Klesp0/Bigtendo-Handheld-SBC/Design/Assets/images/Breakout/breakout_bg.png

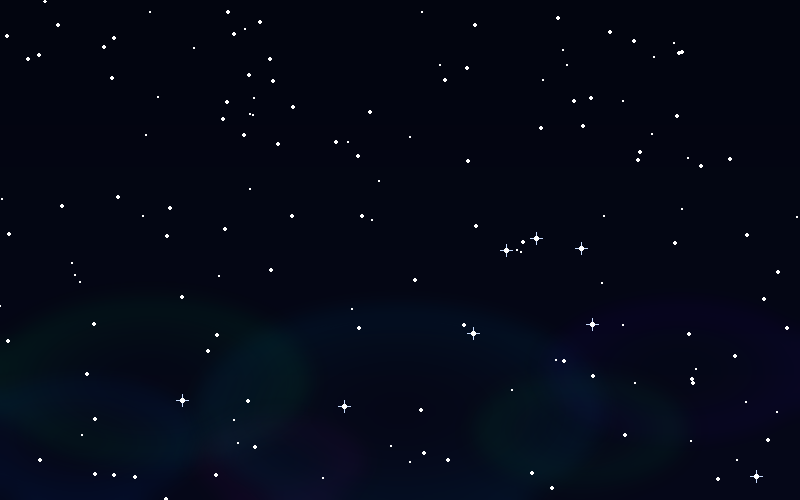
Design/Assets/images/Breakout/breakout_bg.png
