Klesp0/Bigtendo-Handheld-SBC/Design/Assets/images/memory/memory_bg.png

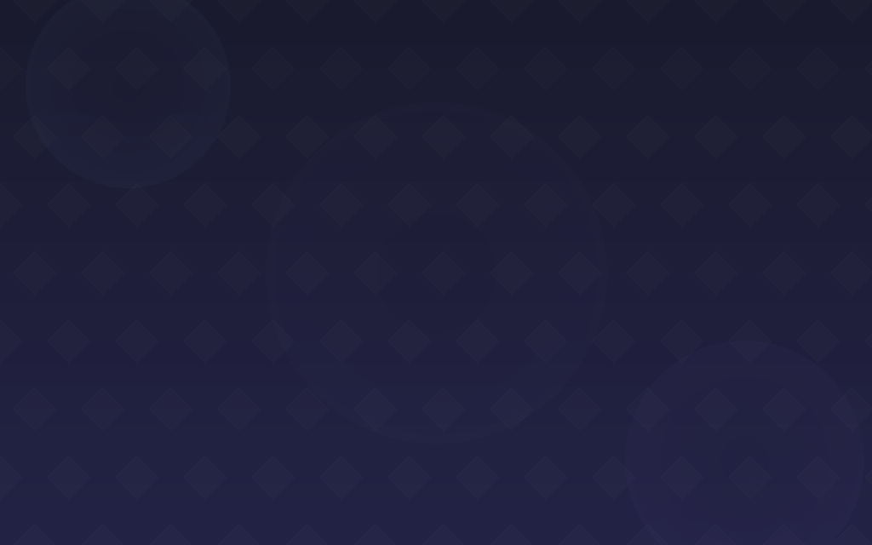
Design/Assets/images/memory/memory_bg.png
