Klesp0/Bigtendo-Handheld-SBC/Media/images/1_ups.png

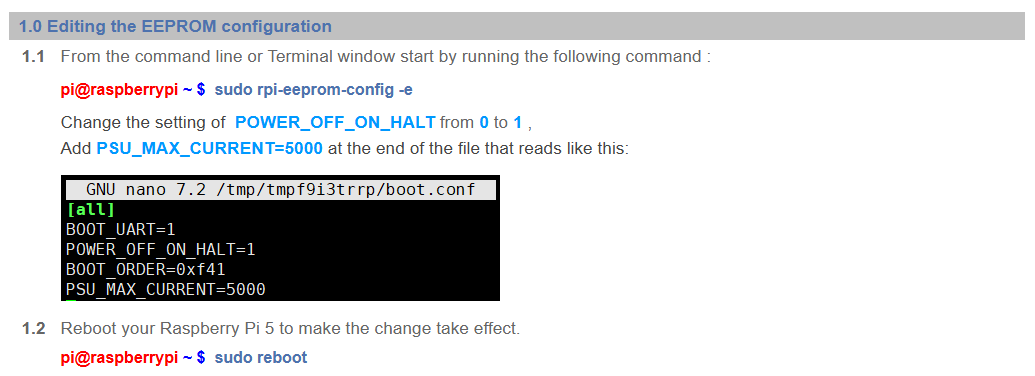
Media/images/1_ups.png
