Klesp0/Bigtendo-Handheld-SBC/Media/images/2_ups.png

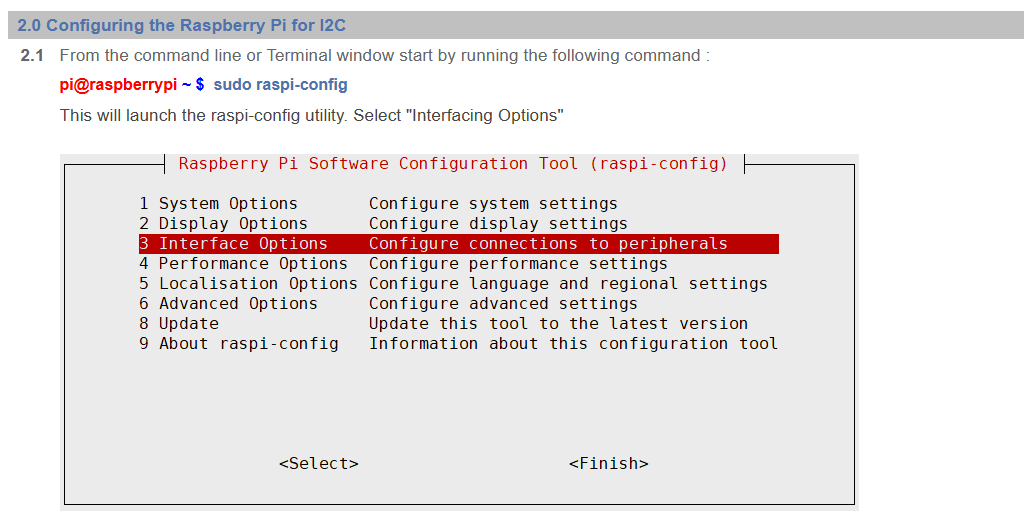
Media/images/2_ups.png
