Klesp0/Bigtendo-Handheld-SBC/Media/images/3_ups.png

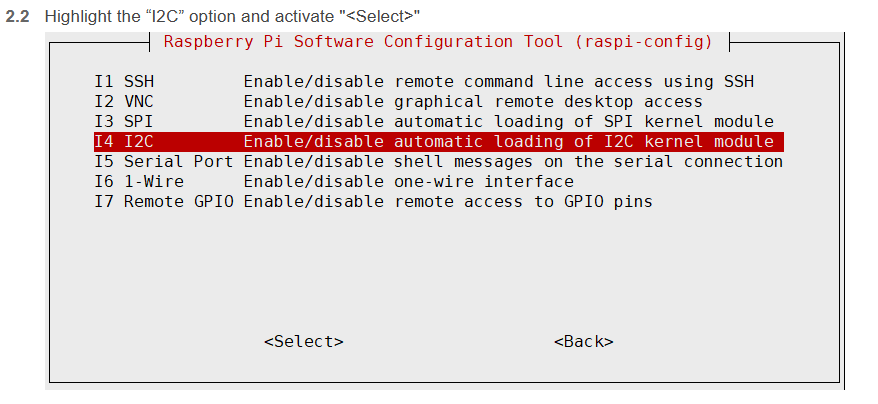
Media/images/3_ups.png
