Klesp0/Bigtendo-Handheld-SBC/Media/images/4_ups.png

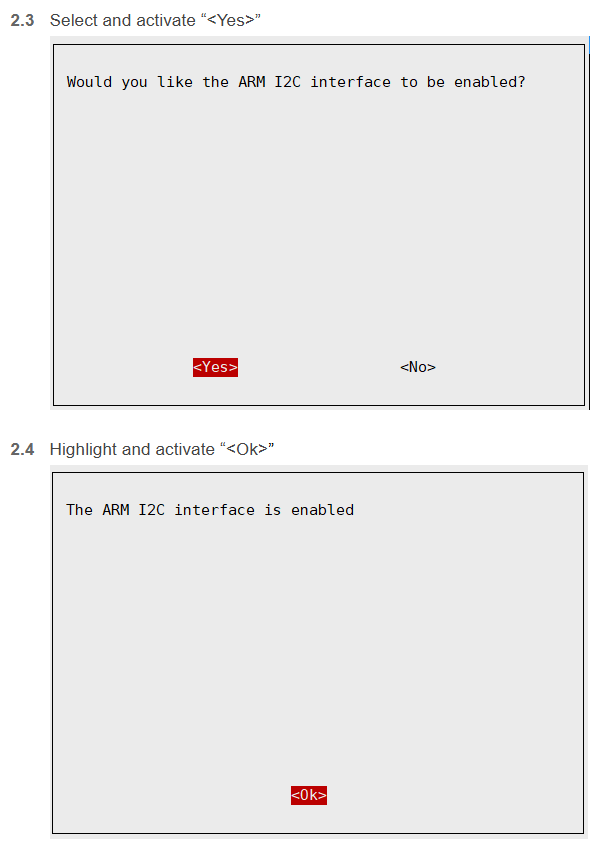
Media/images/4_ups.png
