Klesp0/Bigtendo-Handheld-SBC/Media/images/5_ups.png

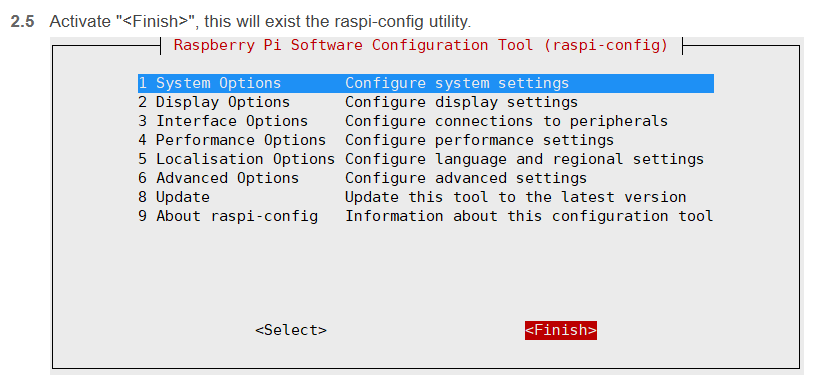
Media/images/5_ups.png
