Klesp0/Bigtendo-Handheld-SBC/Media/images/6_ups.png

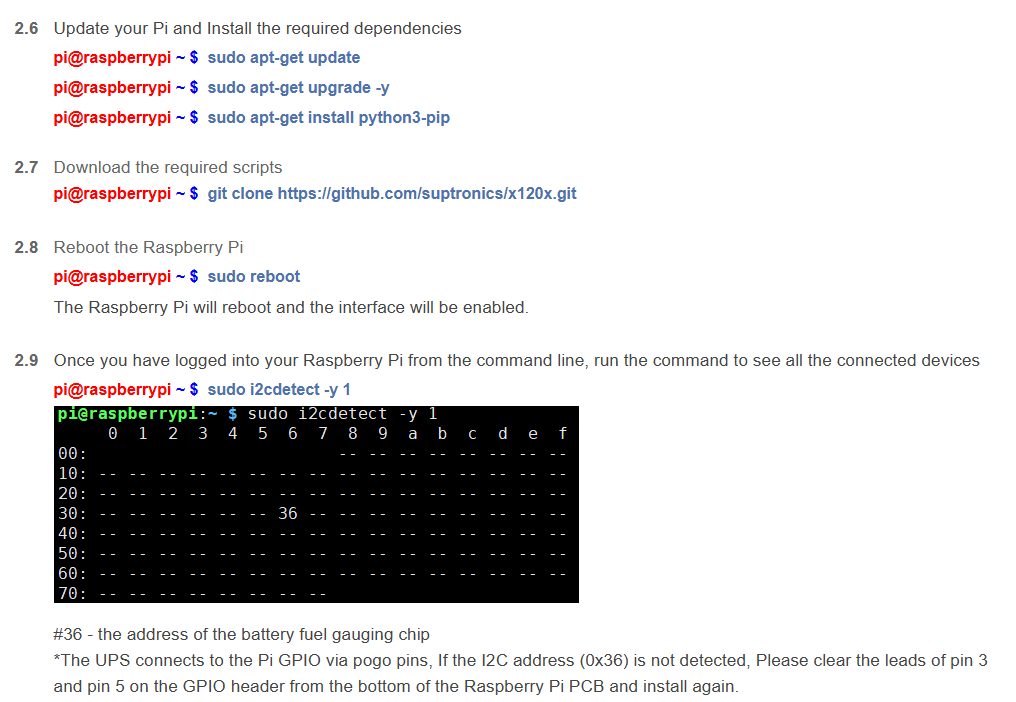
Media/images/6_ups.png
