Klesp0/Bigtendo-Handheld-SBC/Media/images/7_ups.png

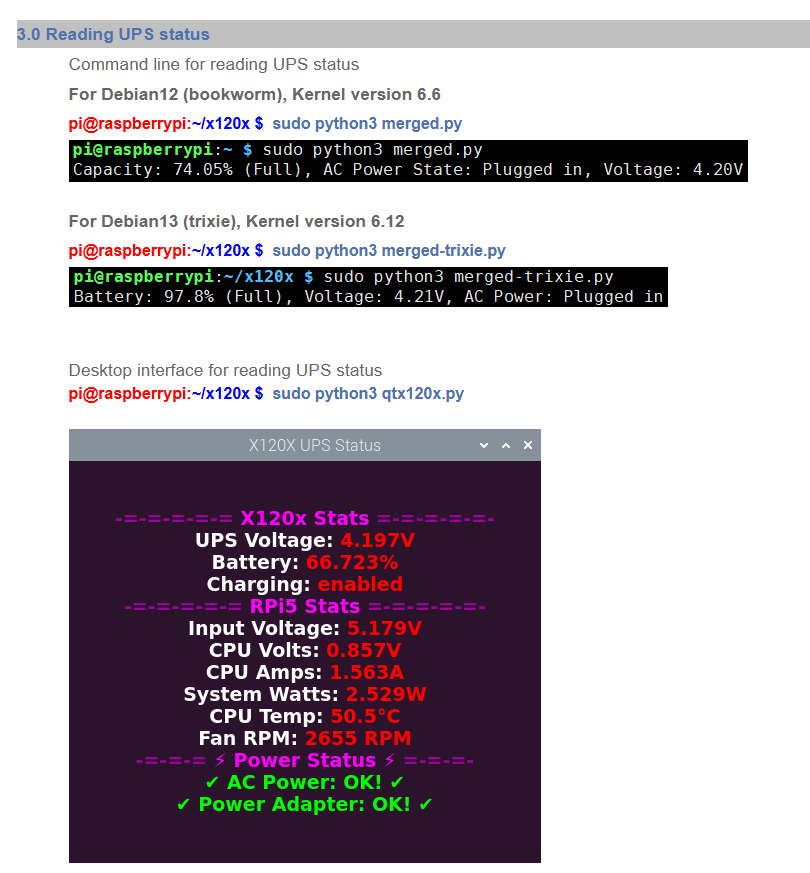
Media/images/7_ups.png
