Klesp0/Bigtendo-Handheld-SBC/Media/images/8_ups.png

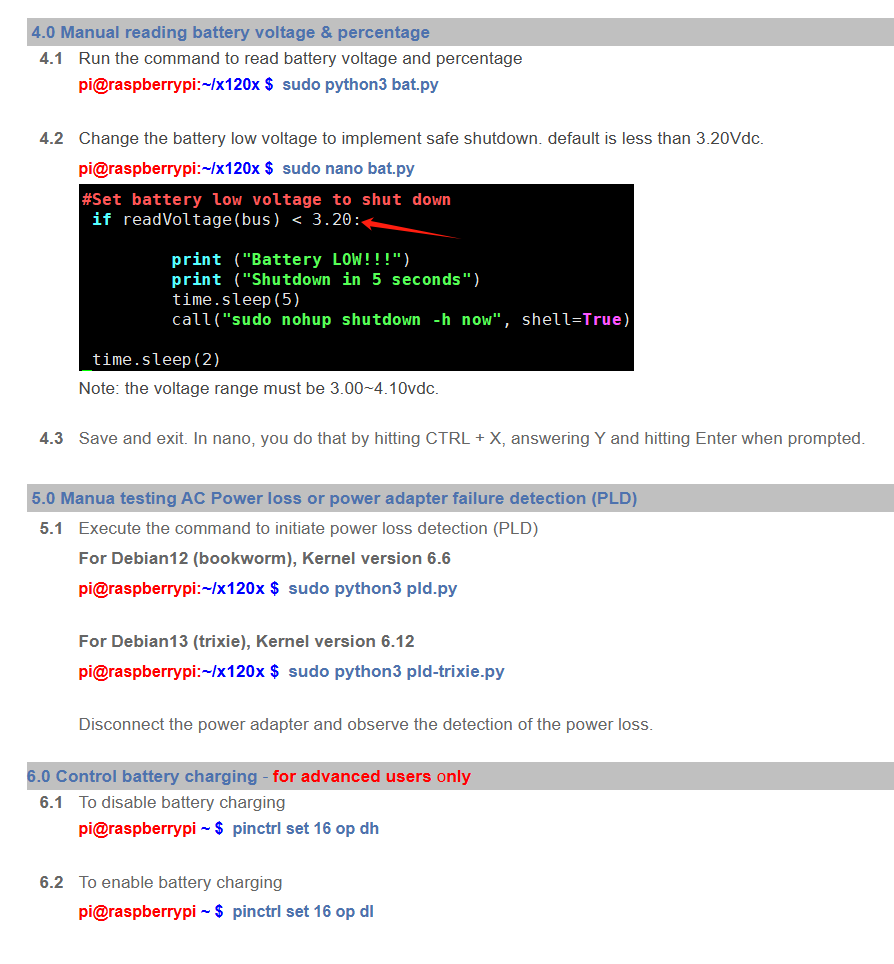
Media/images/8_ups.png
