Klesp0/Bigtendo-Handheld-SBC/Media/images/chuck.jpg

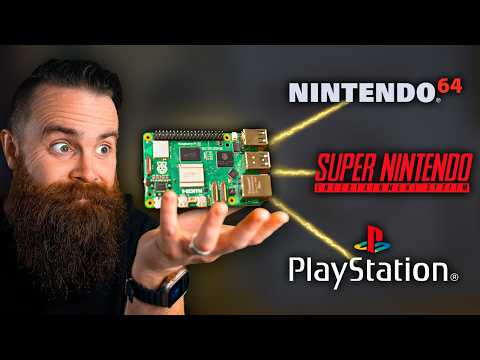
Media/images/chuck.jpg
