Klesp0/Bigtendo-Handheld-SBC/Media/images/imager.png

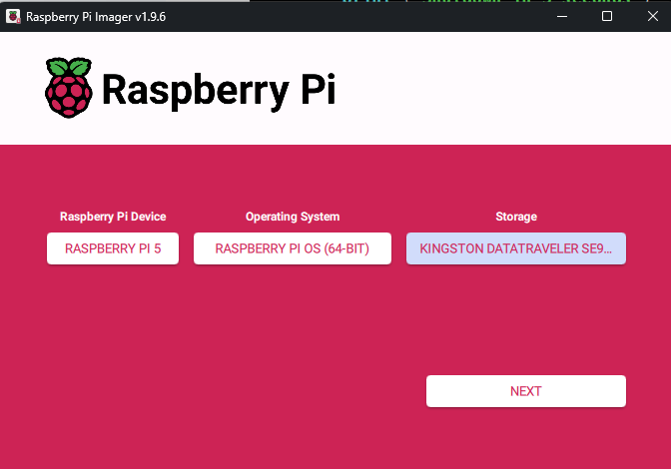
Media/images/imager.png
