Klesp0/Bigtendo-Handheld-SBC/Media/images/Rpi5_pinout.png

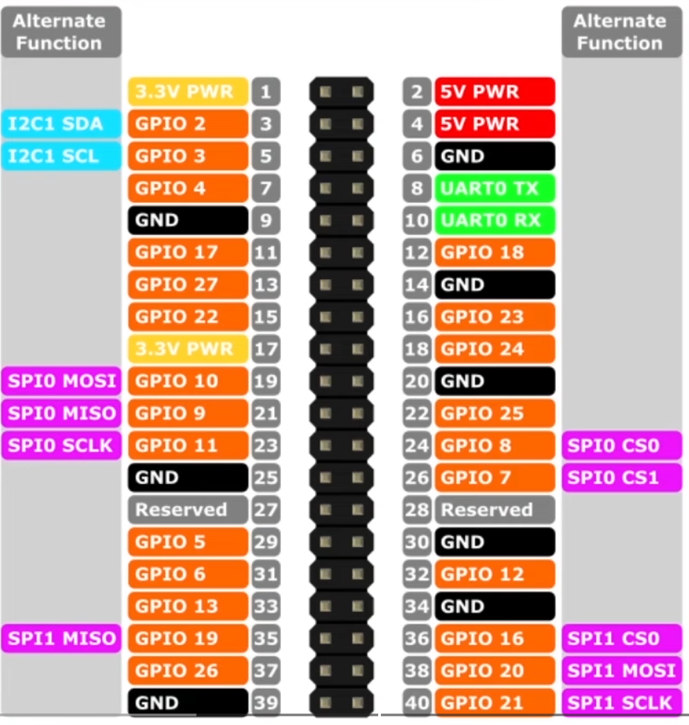
Media/images/Rpi5_pinout.png
