Klesp0/Bigtendo-Handheld-SBC/Media/images/Screenshot 2025-12-04 223239.png

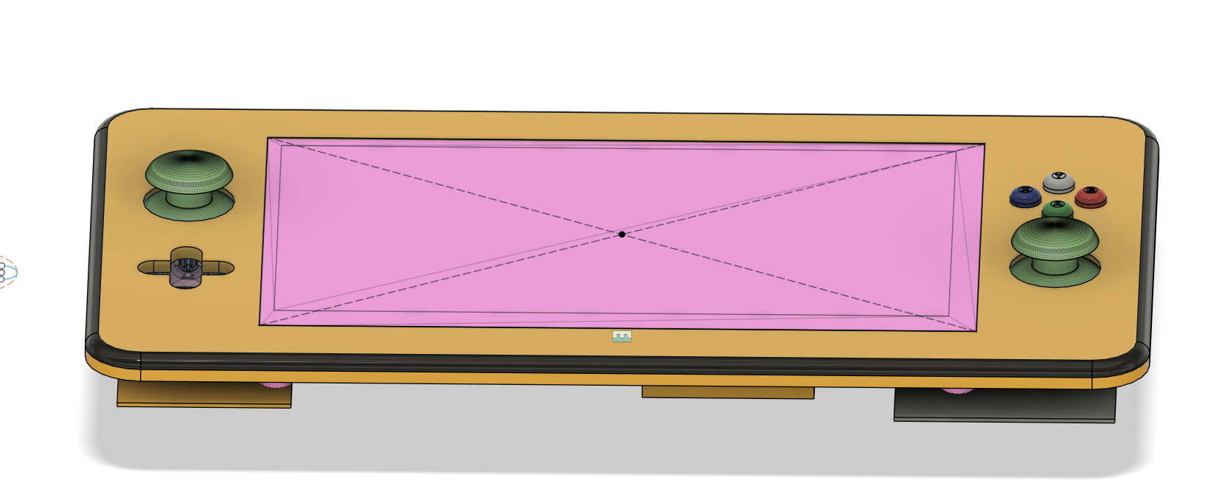
Media/images/Screenshot 2025-12-04 223239.png
