Klesp0/Bigtendo-Handheld-SBC/Media/photos/0d159862-bd19-4e7a-ac6c-457c6c9c0e92.jpg

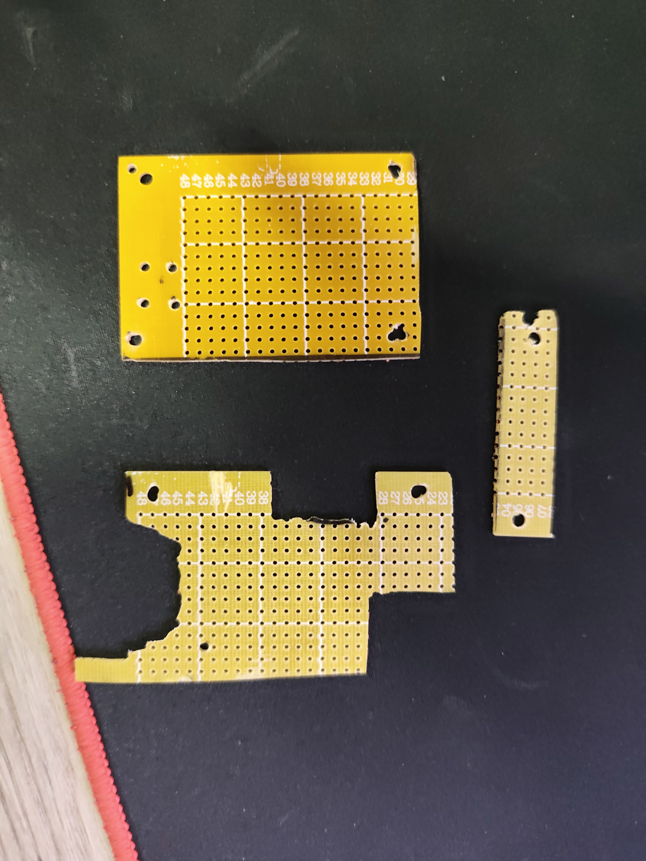
Media/photos/0d159862-bd19-4e7a-ac6c-457c6c9c0e92.jpg
