Klesp0/Bigtendo-Handheld-SBC/Media/photos/1a0360f3-a38d-4172-a27d-07ee18a2b8d9(1).jpg

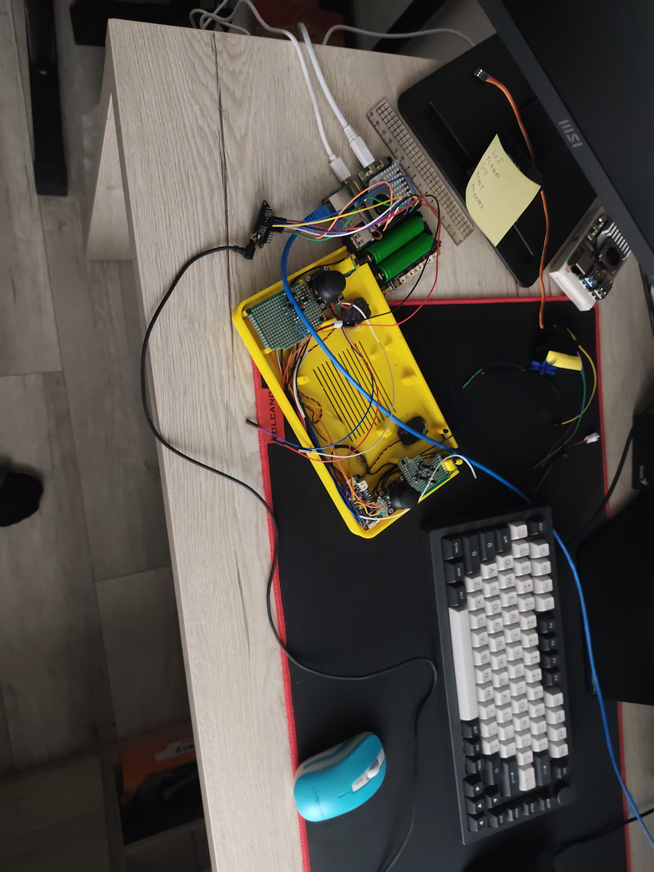
Media/photos/1a0360f3-a38d-4172-a27d-07ee18a2b8d9(1).jpg
