Klesp0/Bigtendo-Handheld-SBC/Media/photos/2c9164c2-df41-48e4-916f-fafe2159fc4d.jpg

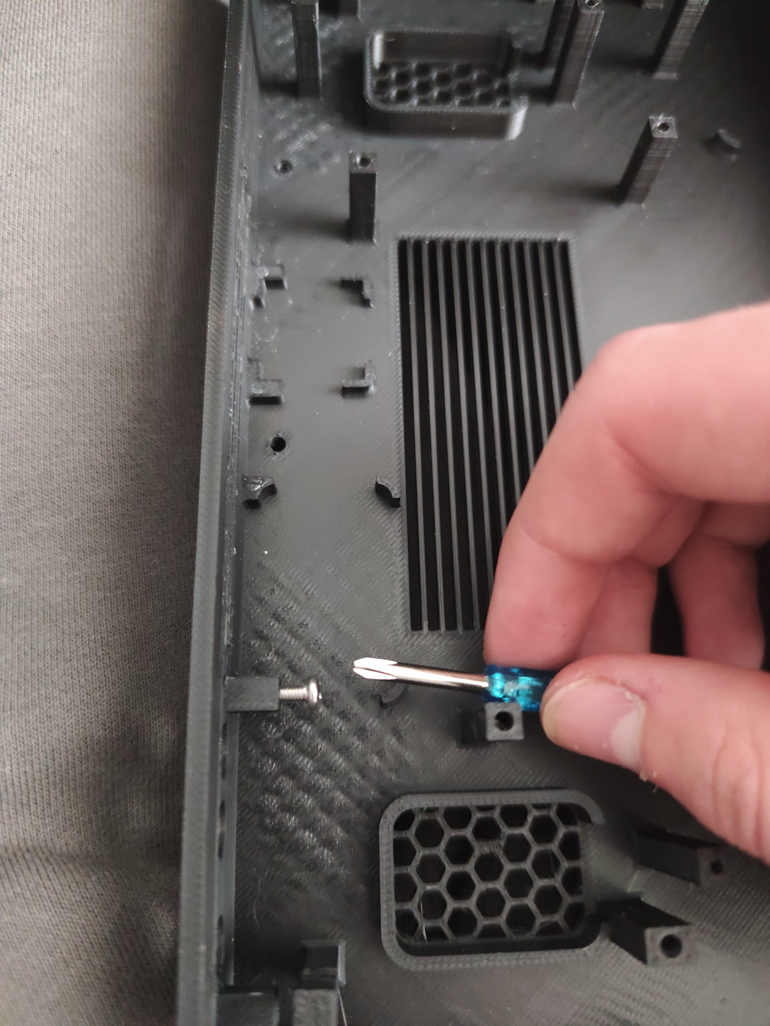
Media/photos/2c9164c2-df41-48e4-916f-fafe2159fc4d.jpg
