Klesp0/Bigtendo-Handheld-SBC/Media/photos/5aacf961-113f-42dd-8feb-71a53d698393.jpg

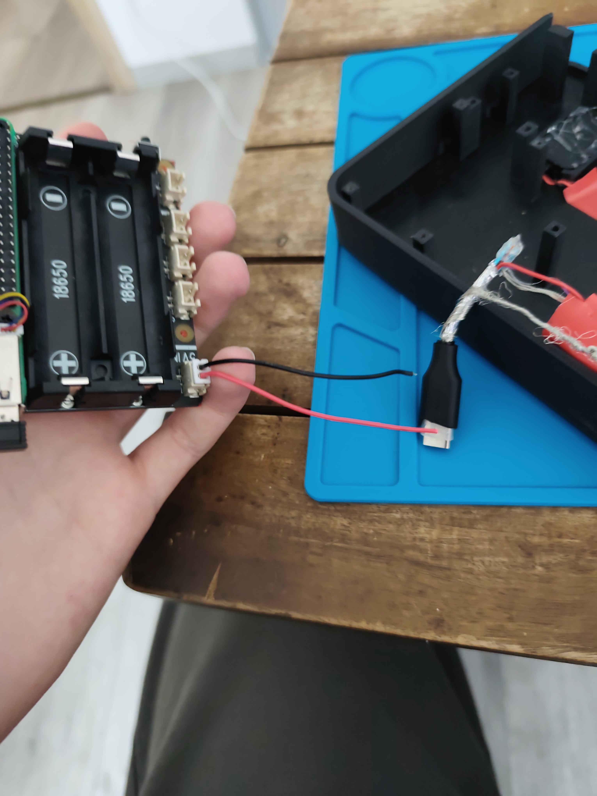
Media/photos/5aacf961-113f-42dd-8feb-71a53d698393.jpg
