Klesp0/Bigtendo-Handheld-SBC/Media/photos/5e09d375-d419-4c3d-b2d1-73679d527c42.jpg

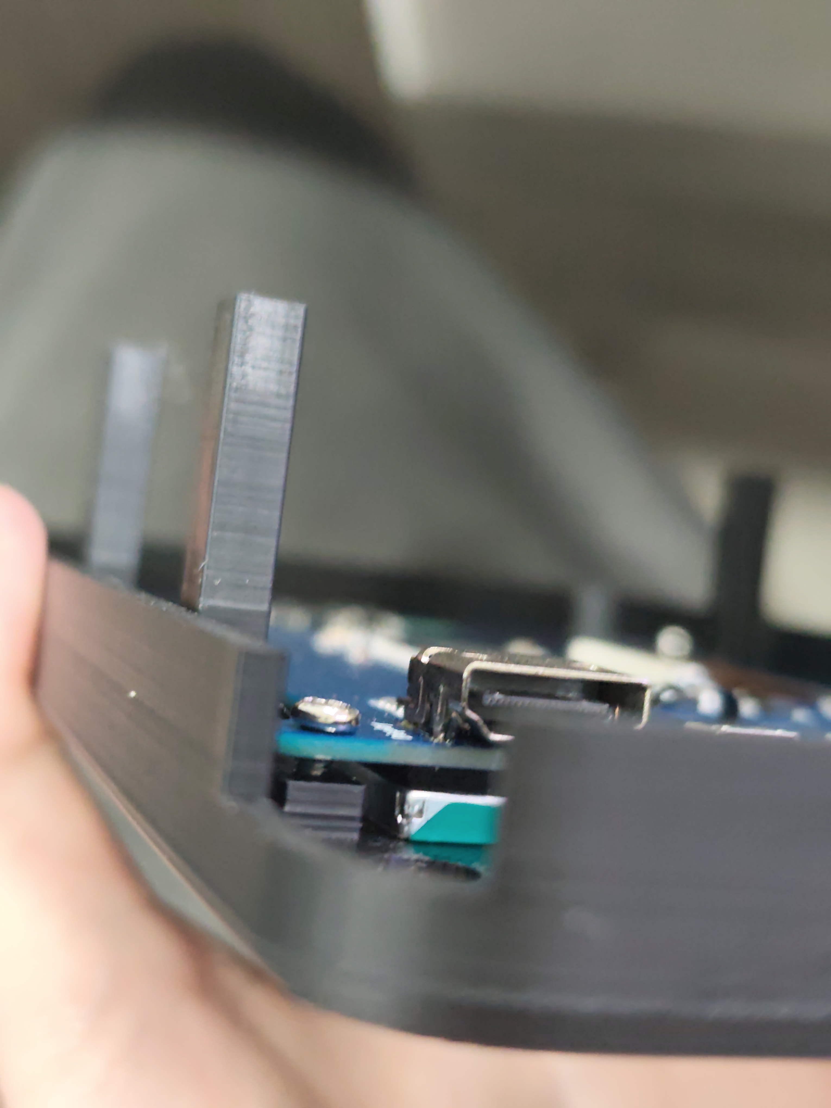
Media/photos/5e09d375-d419-4c3d-b2d1-73679d527c42.jpg
