Klesp0/Bigtendo-Handheld-SBC/Media/photos/6e5a2ec0-2364-49f0-92fe-5897d2cda284.jpg

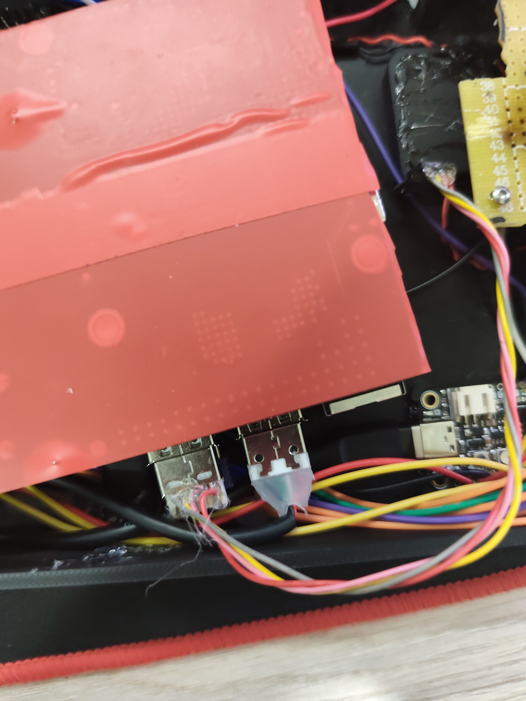
Media/photos/6e5a2ec0-2364-49f0-92fe-5897d2cda284.jpg
