Klesp0/Bigtendo-Handheld-SBC/Media/photos/6e945cf3-38ae-4828-a9d3-f2ff966455ae.jpg

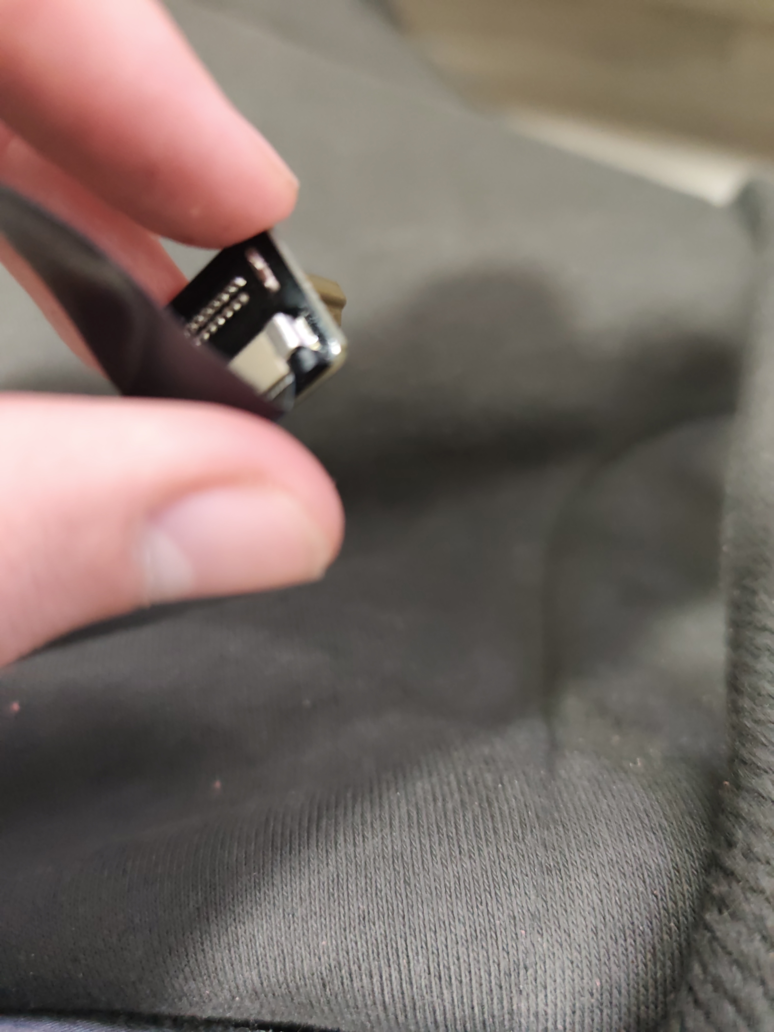
Media/photos/6e945cf3-38ae-4828-a9d3-f2ff966455ae.jpg
