Klesp0/Bigtendo-Handheld-SBC/Media/photos/46b99d0f-3195-408c-8193-283539404b6c.jpg

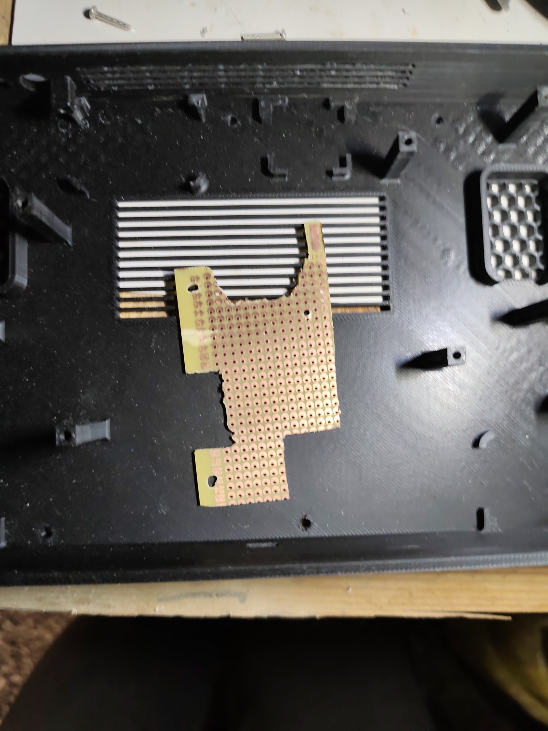
Media/photos/46b99d0f-3195-408c-8193-283539404b6c.jpg
