Klesp0/Bigtendo-Handheld-SBC/Media/photos/55b0e54c-f542-49ae-9d47-5be7d64822e2.jpg

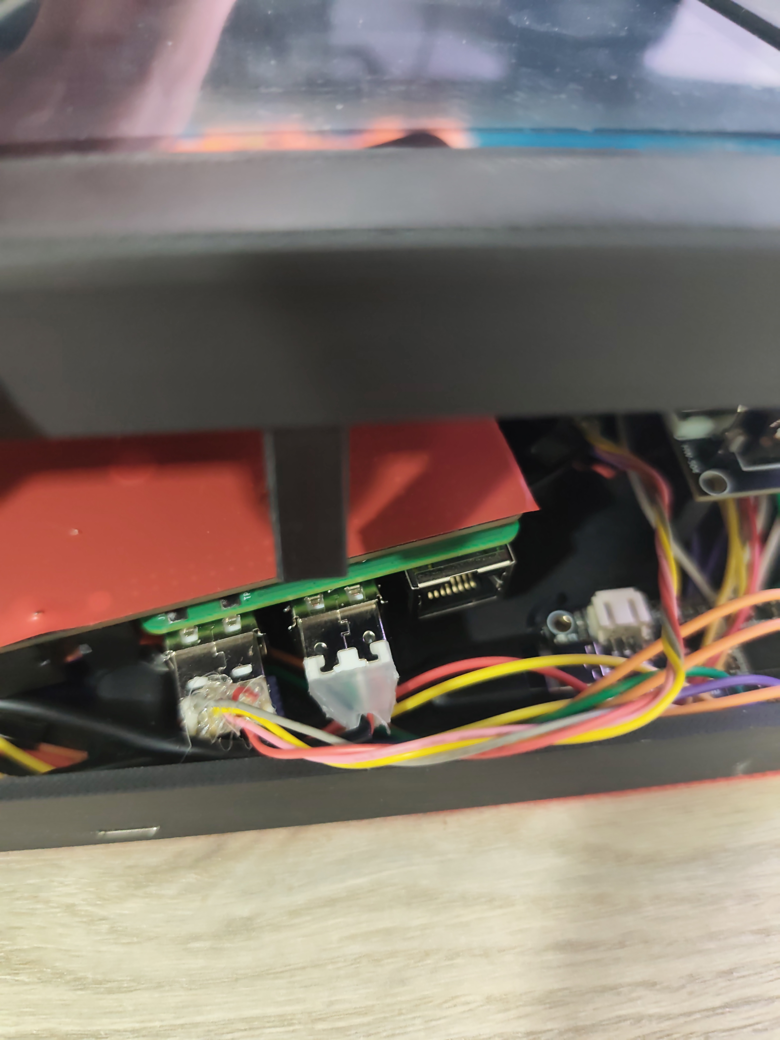
Media/photos/55b0e54c-f542-49ae-9d47-5be7d64822e2.jpg
