Klesp0/Bigtendo-Handheld-SBC/Media/photos/63fe22ae-a2fc-4c9e-bf27-66a3d39b91c6.jpg

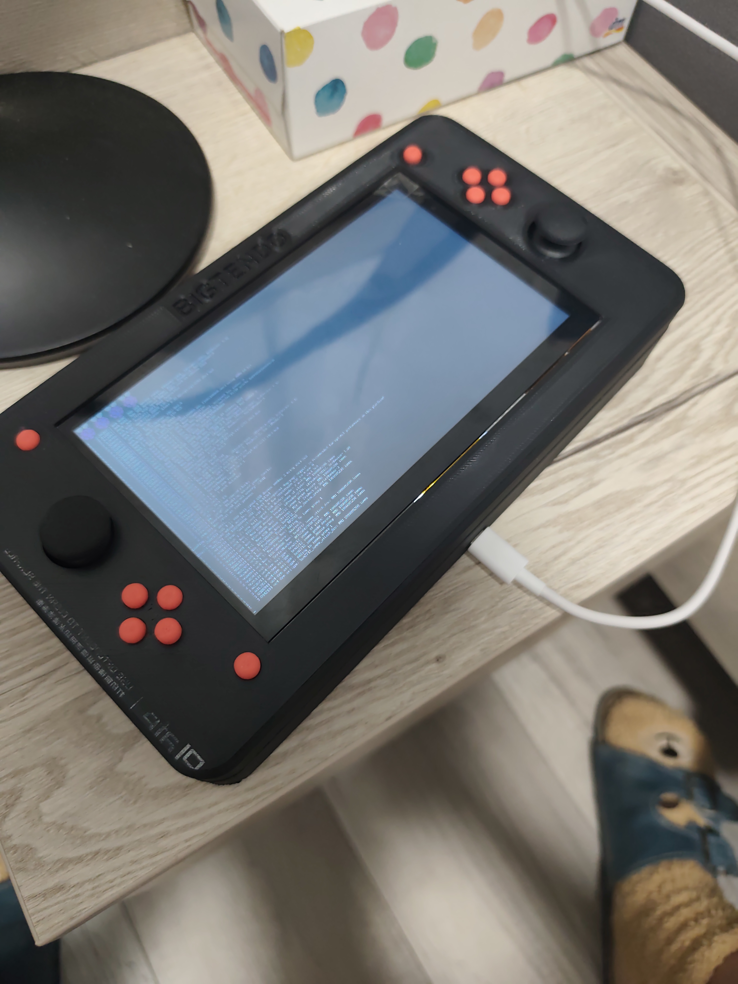
Media/photos/63fe22ae-a2fc-4c9e-bf27-66a3d39b91c6.jpg
