Klesp0/Bigtendo-Handheld-SBC/Media/photos/68ed0358-8793-4e74-b9dc-9e63b9d81c03.jpg

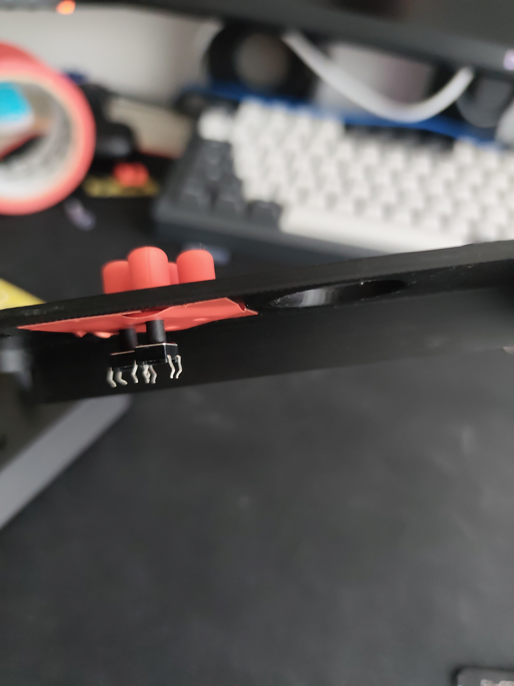
Media/photos/68ed0358-8793-4e74-b9dc-9e63b9d81c03.jpg
