Klesp0/Bigtendo-Handheld-SBC/Media/photos/849dee18-2907-47e5-b8df-e42aead211ff.jpg

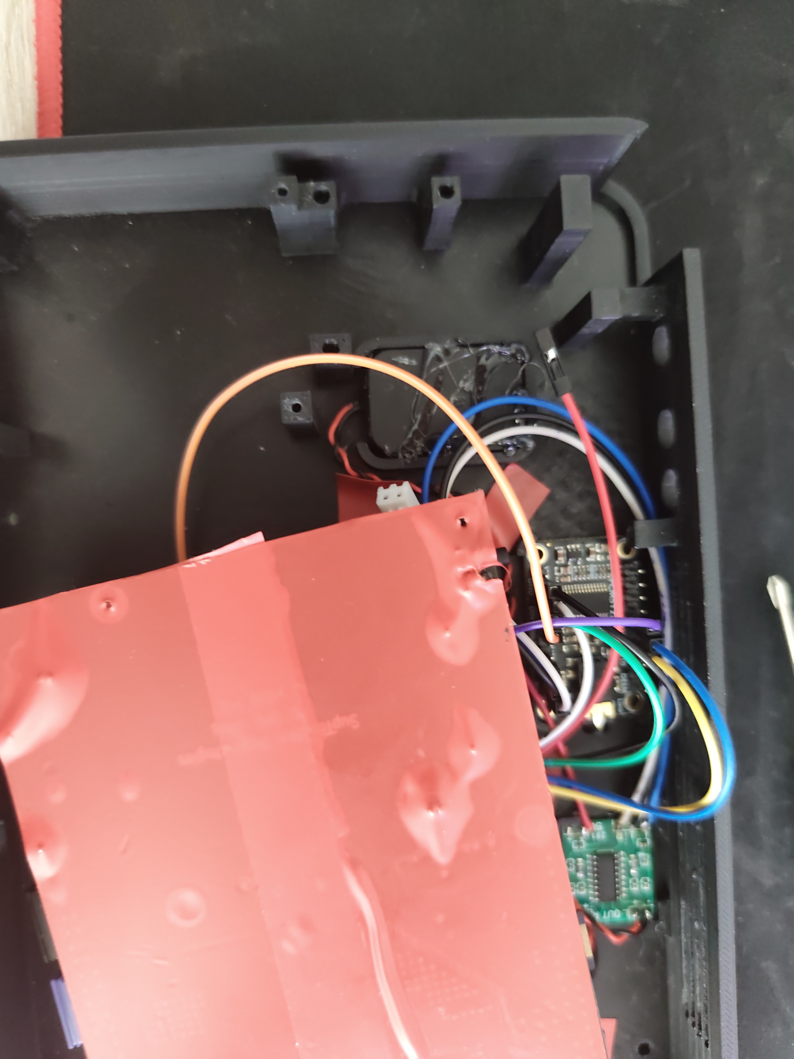
Media/photos/849dee18-2907-47e5-b8df-e42aead211ff.jpg
