Klesp0/Bigtendo-Handheld-SBC/Media/photos/20911a5c-09a5-460e-9626-143bd7f02a5c.jpg

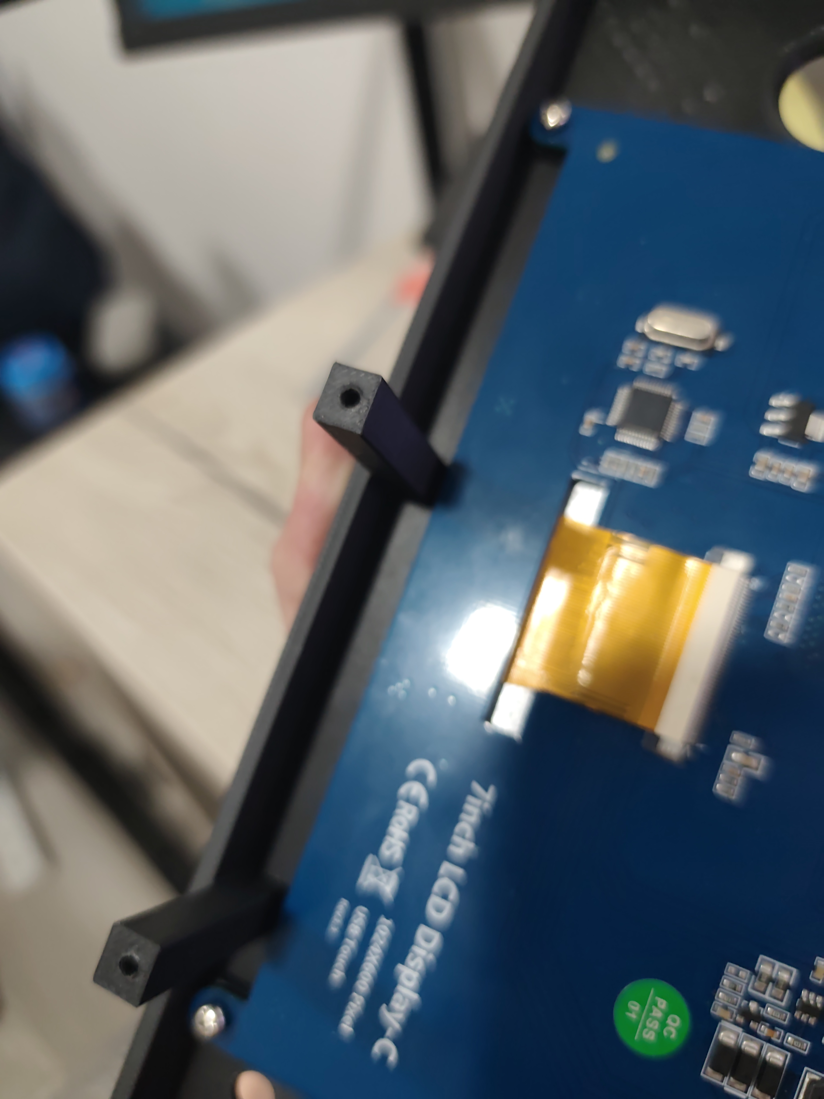
Media/photos/20911a5c-09a5-460e-9626-143bd7f02a5c.jpg
