Klesp0/Bigtendo-Handheld-SBC/Media/photos/20260312_102649.jpg

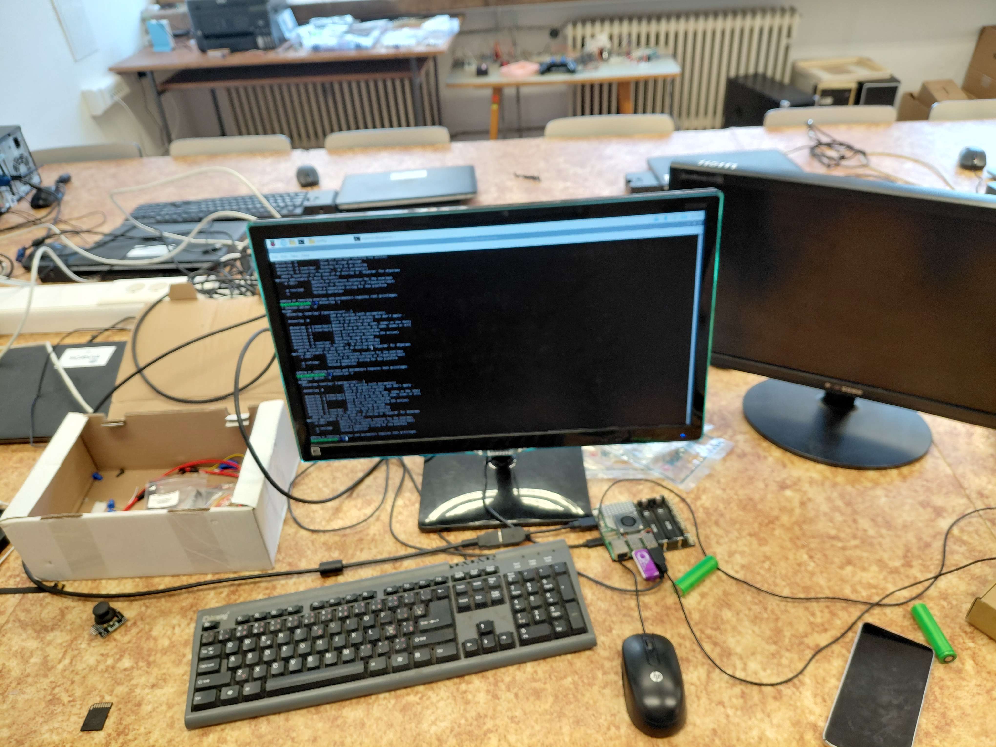
Media/photos/20260312_102649.jpg
