Klesp0/Bigtendo-Handheld-SBC/Media/photos/bdb9f96a-c696-4ba6-920f-6b57244c4c61.jpg

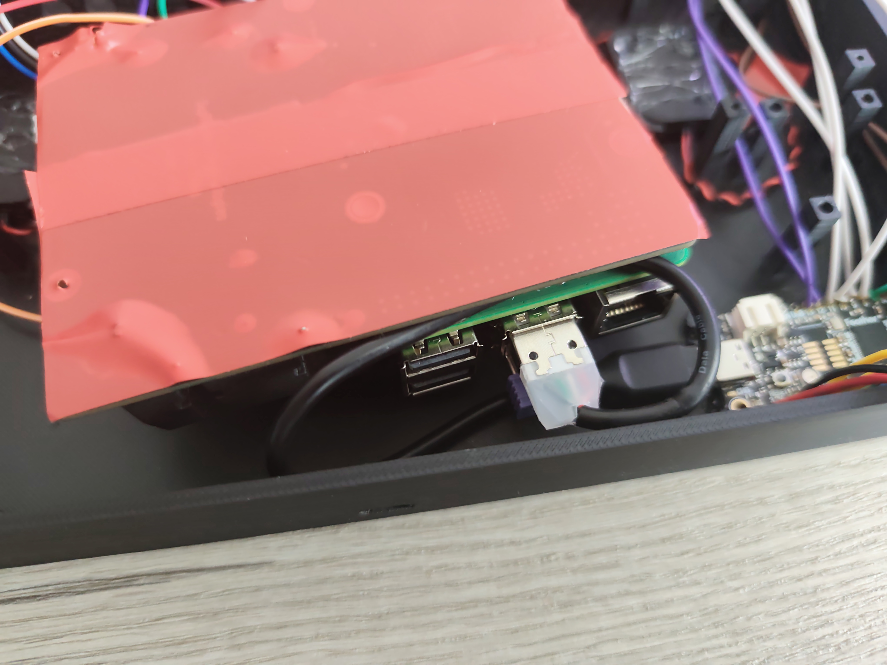
Media/photos/bdb9f96a-c696-4ba6-920f-6b57244c4c61.jpg
