Klesp0/Bigtendo-Handheld-SBC/Media/photos/c5f9a370-ef26-4754-a01f-f3f65732aec8(1).jpg

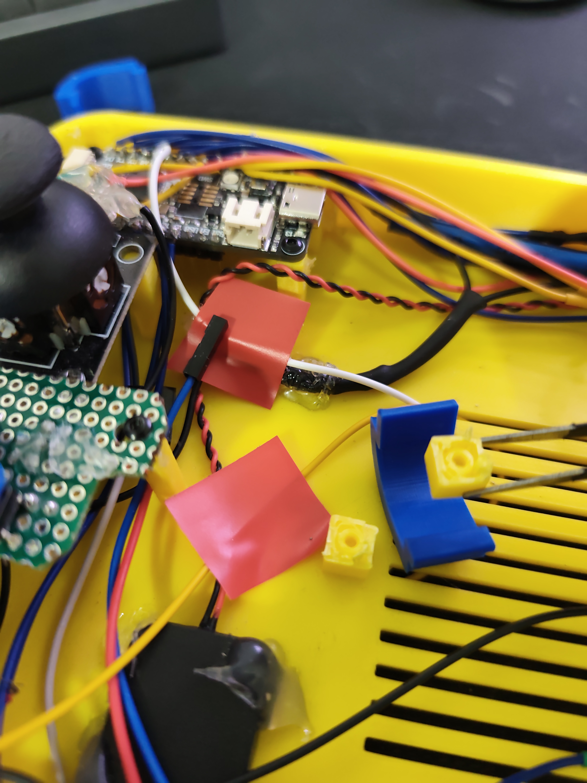
Media/photos/c5f9a370-ef26-4754-a01f-f3f65732aec8(1).jpg
