Klesp0/Bigtendo-Handheld-SBC/Media/photos/c06b81f2-fac6-4397-86d1-96d78a3ae781.jpg

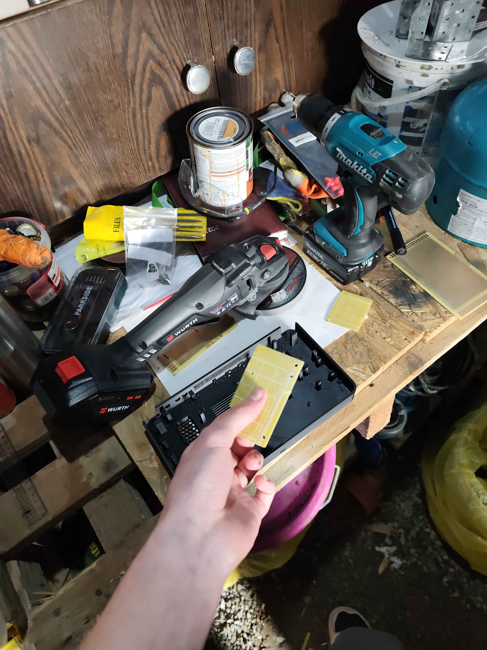
Media/photos/c06b81f2-fac6-4397-86d1-96d78a3ae781.jpg
