Klesp0/Bigtendo-Handheld-SBC/Media/photos/ca927152-84cd-4235-90fc-1009e0bbeaf4.jpg

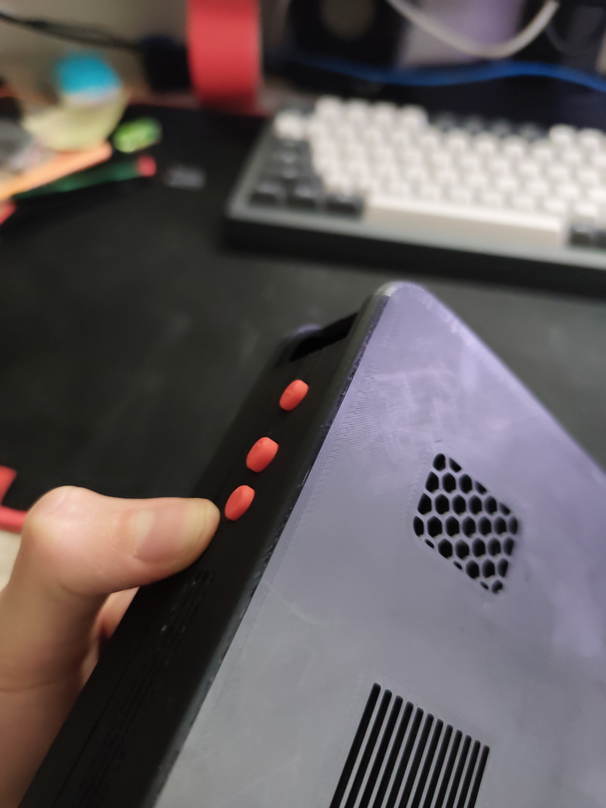
Media/photos/ca927152-84cd-4235-90fc-1009e0bbeaf4.jpg
