Klesp0/Bigtendo-Handheld-SBC/Media/photos/cecb70cf-d62d-4f64-a7af-b3d049f17aff.jpg

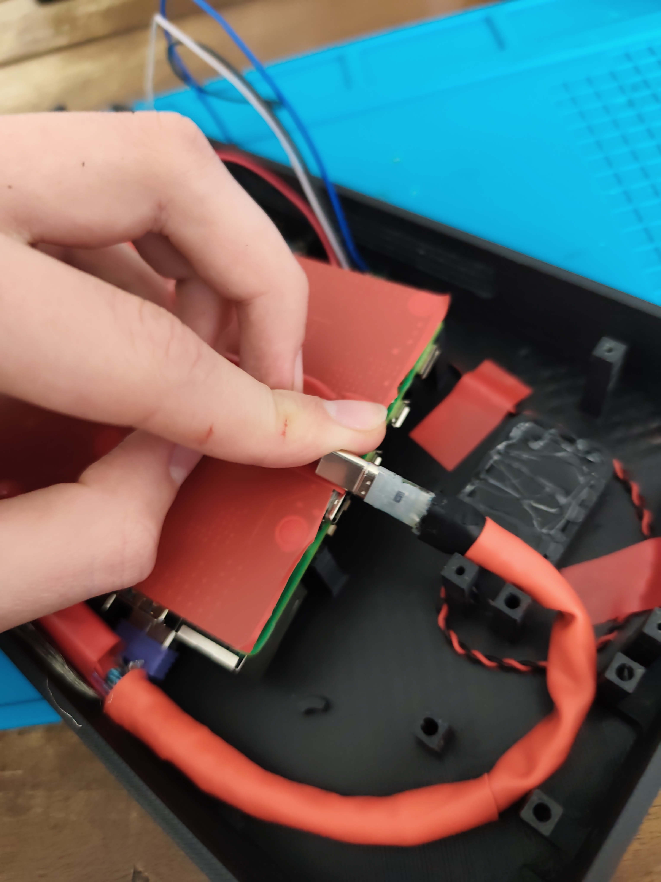
Media/photos/cecb70cf-d62d-4f64-a7af-b3d049f17aff.jpg
