Klesp0/Bigtendo-Handheld-SBC/Media/photos/cf581f9f-bc78-4fae-b57e-3b8caa427790.jpg

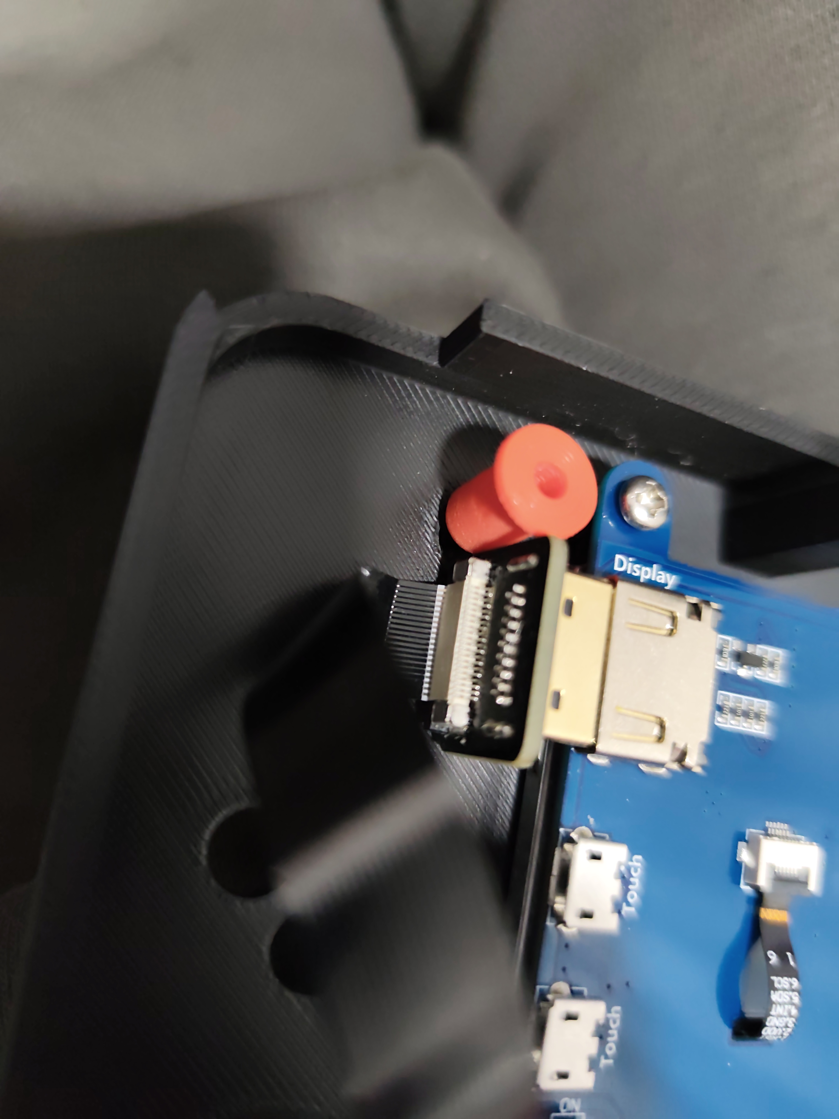
Media/photos/cf581f9f-bc78-4fae-b57e-3b8caa427790.jpg
