Klesp0/Bigtendo-Handheld-SBC/Media/photos/d723101f-bc0a-4b1f-b0e9-9cadc9bb3473.jpg

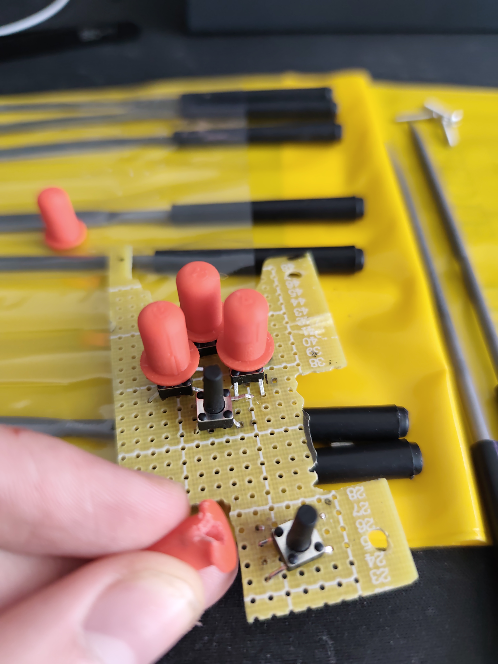
Media/photos/d723101f-bc0a-4b1f-b0e9-9cadc9bb3473.jpg
