Klesp0/Bigtendo-Handheld-SBC/Media/photos/ed0d629f-f254-4d7c-ab42-fab773d44528(1).jpg

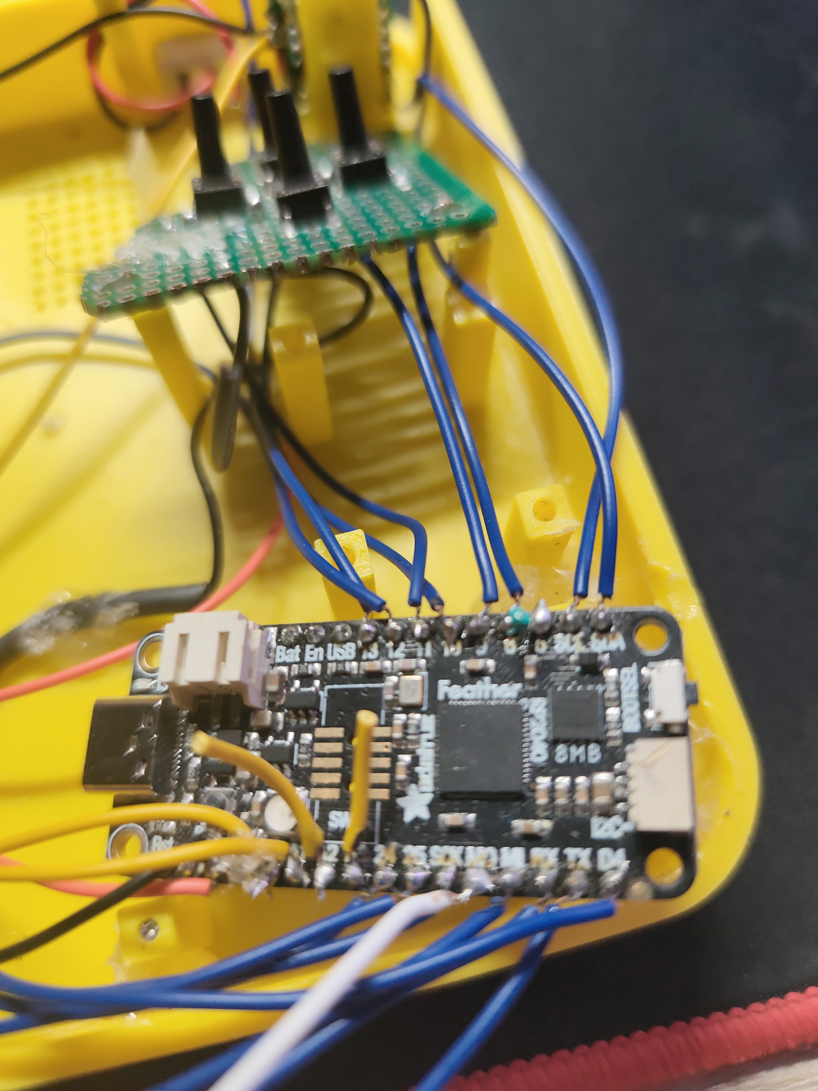
Media/photos/ed0d629f-f254-4d7c-ab42-fab773d44528(1).jpg
