Klesp0/Bigtendo-Handheld-SBC/Media/photos/IMG_20260208_225611(1).jpg

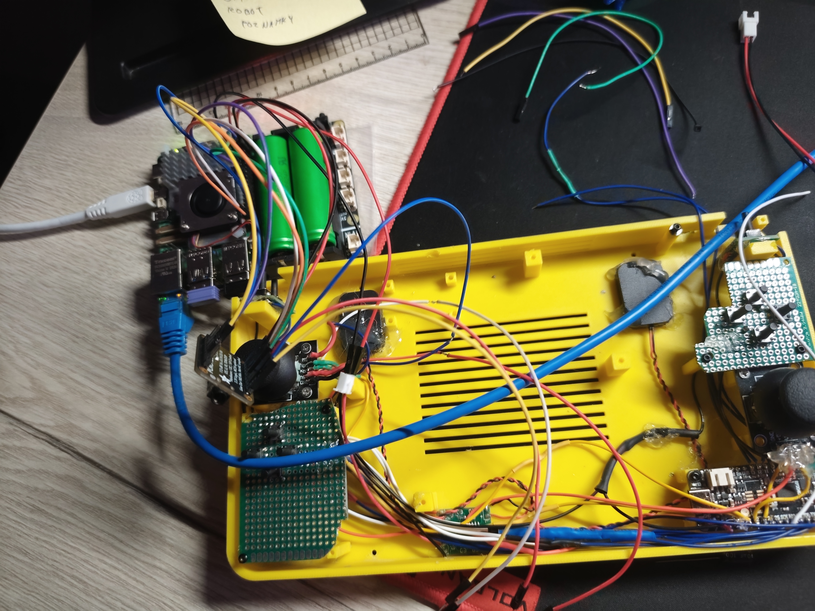
Media/photos/IMG_20260208_225611(1).jpg
