Klesp0/Bigtendo-Handheld-SBC/Media/photos/IMG_20260212_185116(1).jpg

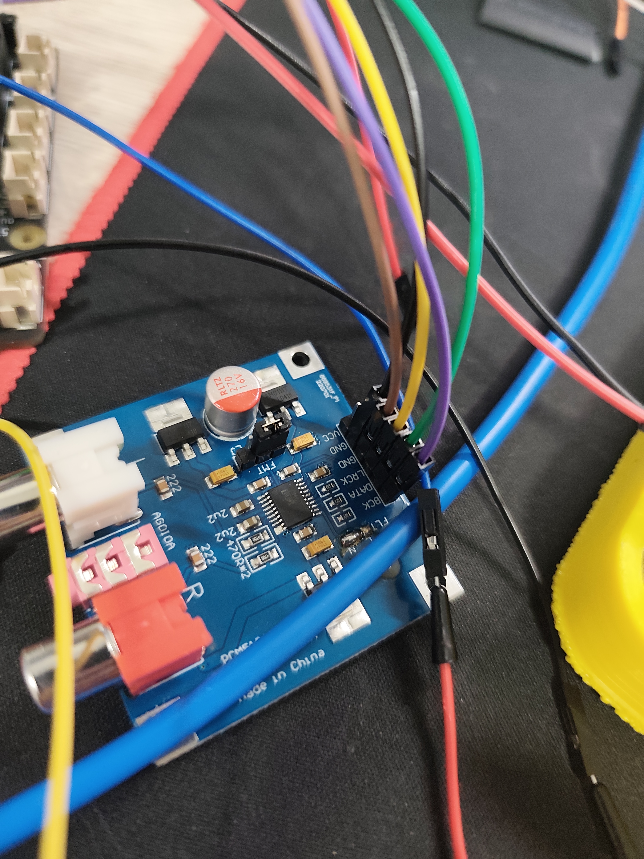
Media/photos/IMG_20260212_185116(1).jpg
