Klesp0/Bigtendo-Handheld-SBC/Media/photos/IMG_20260217_225508(1).jpg

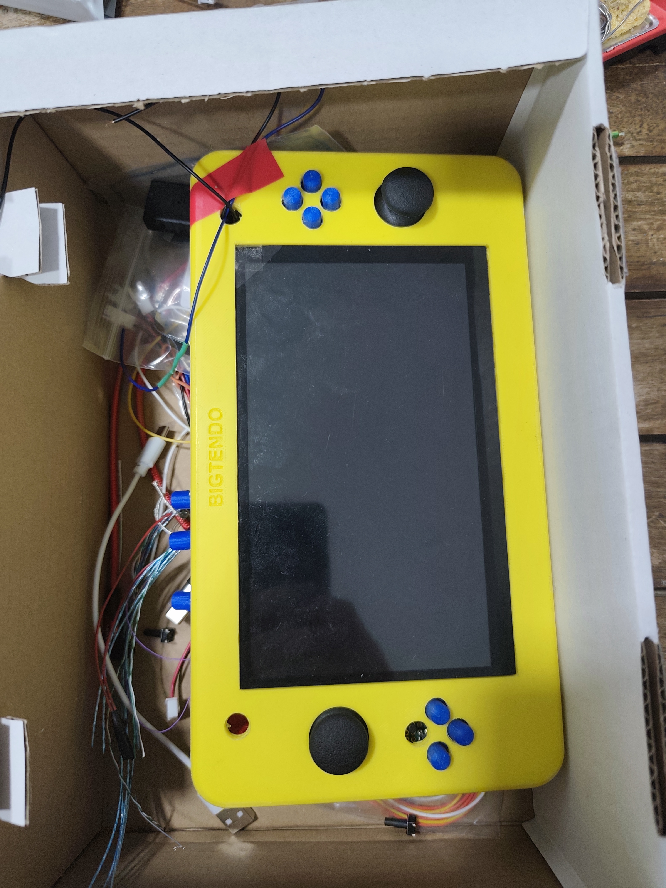
Media/photos/IMG_20260217_225508(1).jpg
