Klesp0/Bigtendo-Handheld-SBC/Media/photos/IMG_20260222_182543(1).jpg

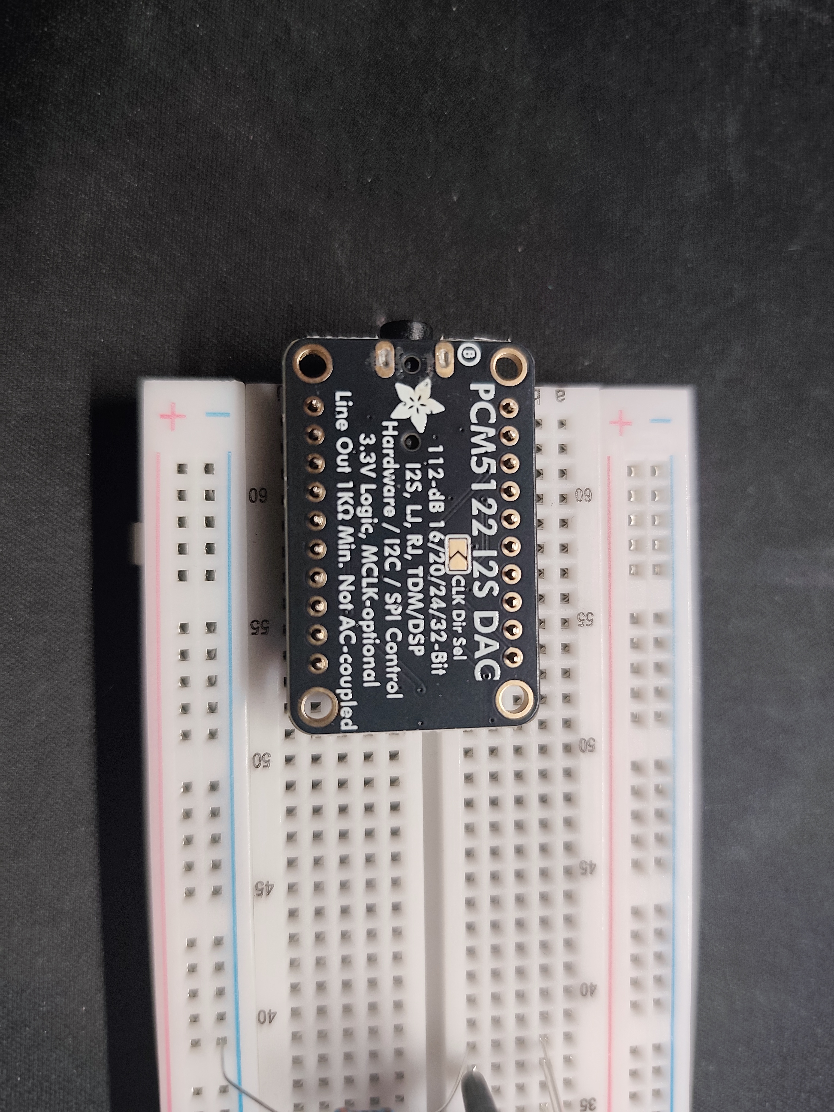
Media/photos/IMG_20260222_182543(1).jpg
