Klesp0/Bigtendo-Handheld-SBC/Media/photos/IMG_20260312_103524.jpg

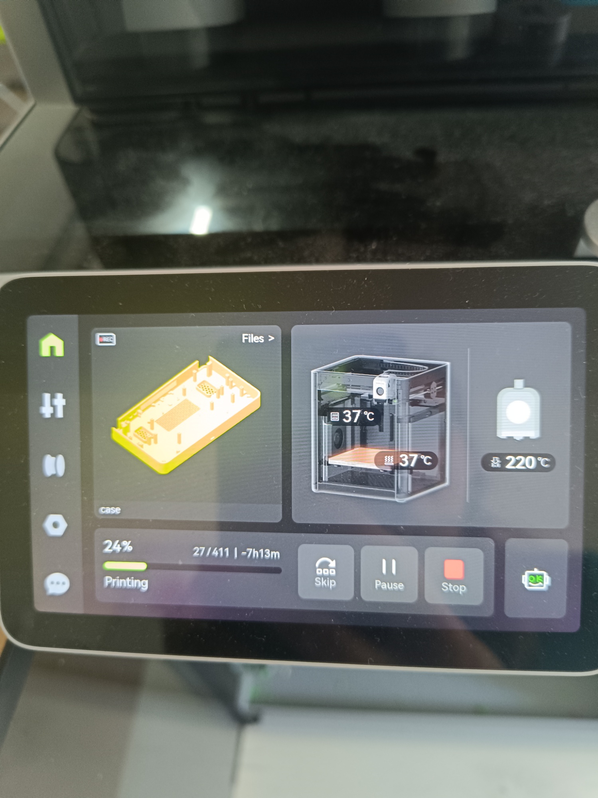
Media/photos/IMG_20260312_103524.jpg
