Klesp0/Bigtendo-Handheld-SBC/Media/photos/IMG_20260313_091914.jpg

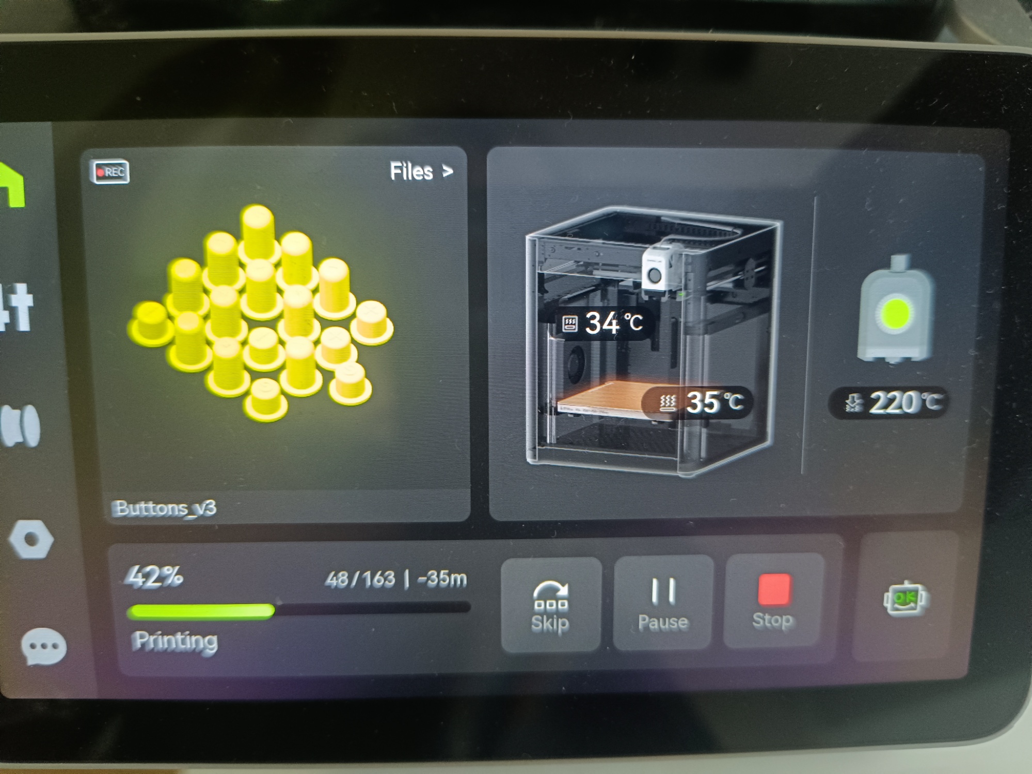
Media/photos/IMG_20260313_091914.jpg
