Klesp0/Bigtendo-Handheld-SBC/Media/photos/IMG_20260313_091924.jpg

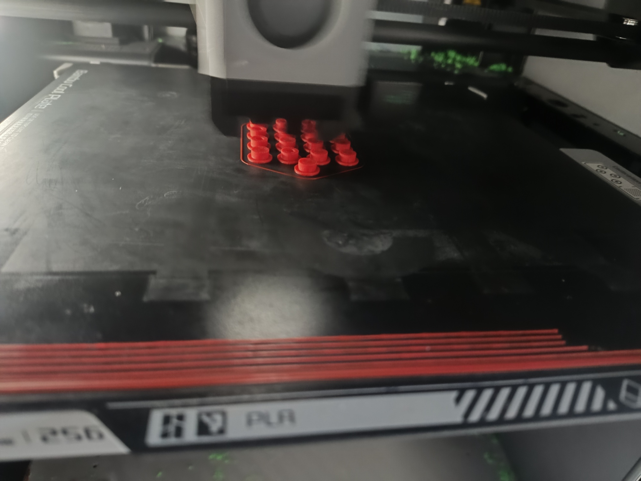
Media/photos/IMG_20260313_091924.jpg
