Klesp0/Bigtendo-Handheld-SBC/Media/photos/IMG_20260313_095501.jpg

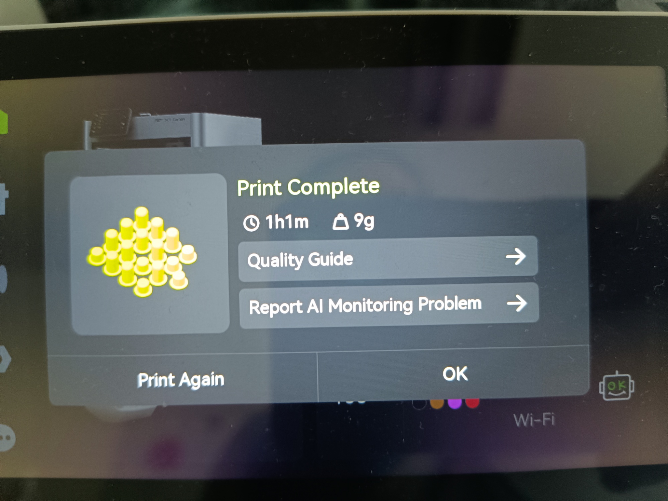
Media/photos/IMG_20260313_095501.jpg
