Klesp0/Bigtendo-Handheld-SBC/Media/photos/IMG_20260313_210248.jpg

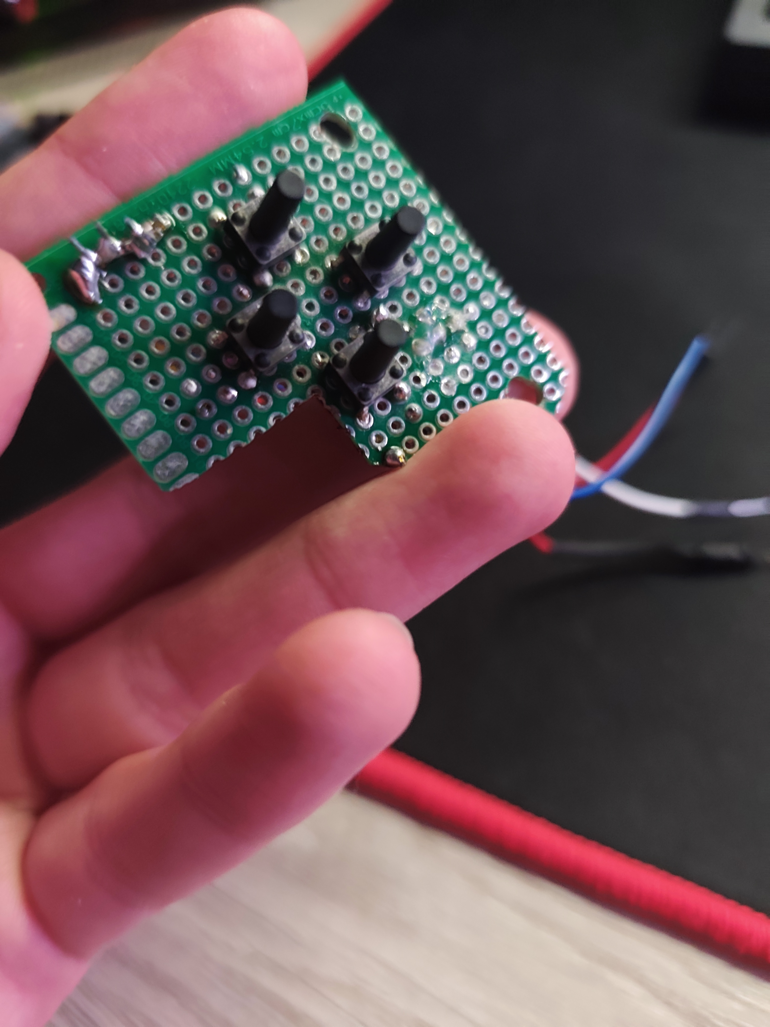
Media/photos/IMG_20260313_210248.jpg
