Klesp0/Bigtendo-Handheld-SBC/Media/photos/IMG_20260314_113954.jpg

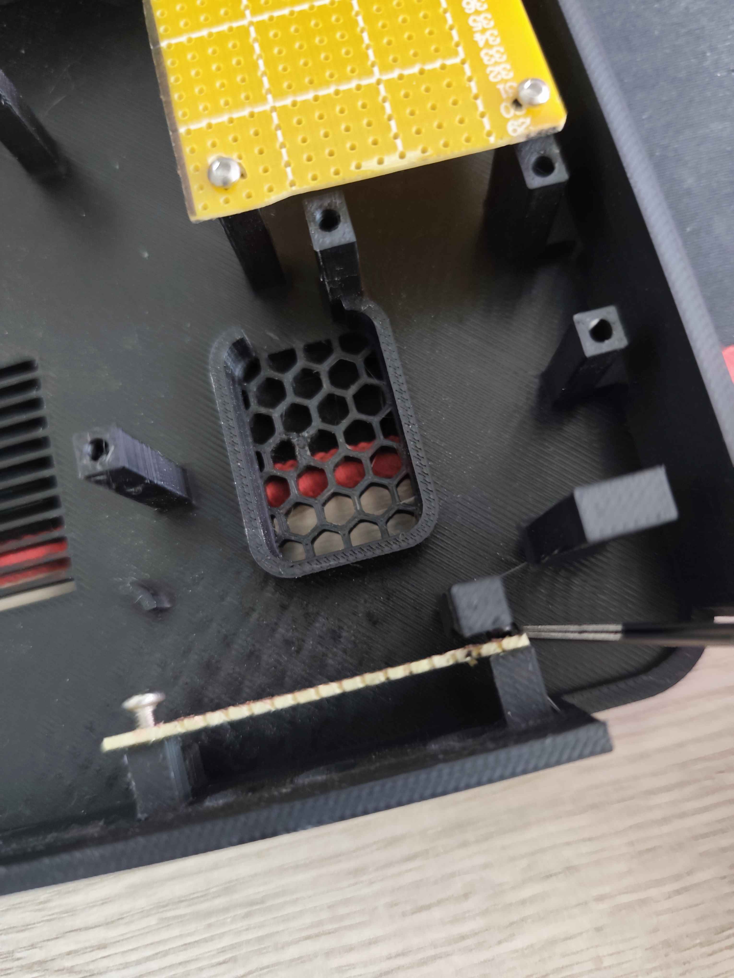
Media/photos/IMG_20260314_113954.jpg
