Klesp0/Bigtendo-Handheld-SBC/Media/photos/IMG_20260314_123427.jpg

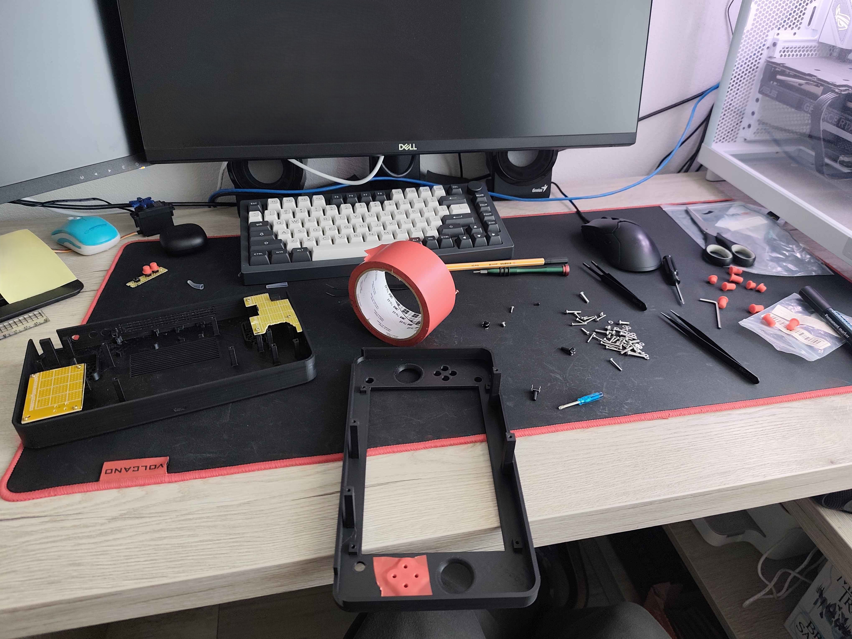
Media/photos/IMG_20260314_123427.jpg
