Klesp0/Bigtendo-Handheld-SBC/Media/photos/IMG_20260314_123434.jpg

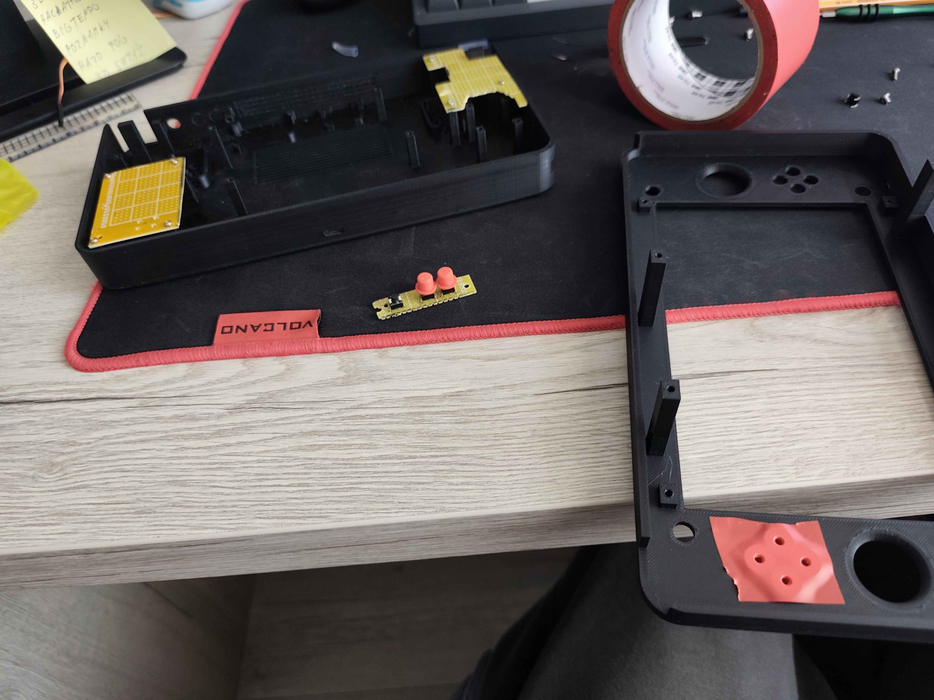
Media/photos/IMG_20260314_123434.jpg
