Klesp0/Bigtendo-Handheld-SBC/Media/photos/IMG_20260314_141306.jpg

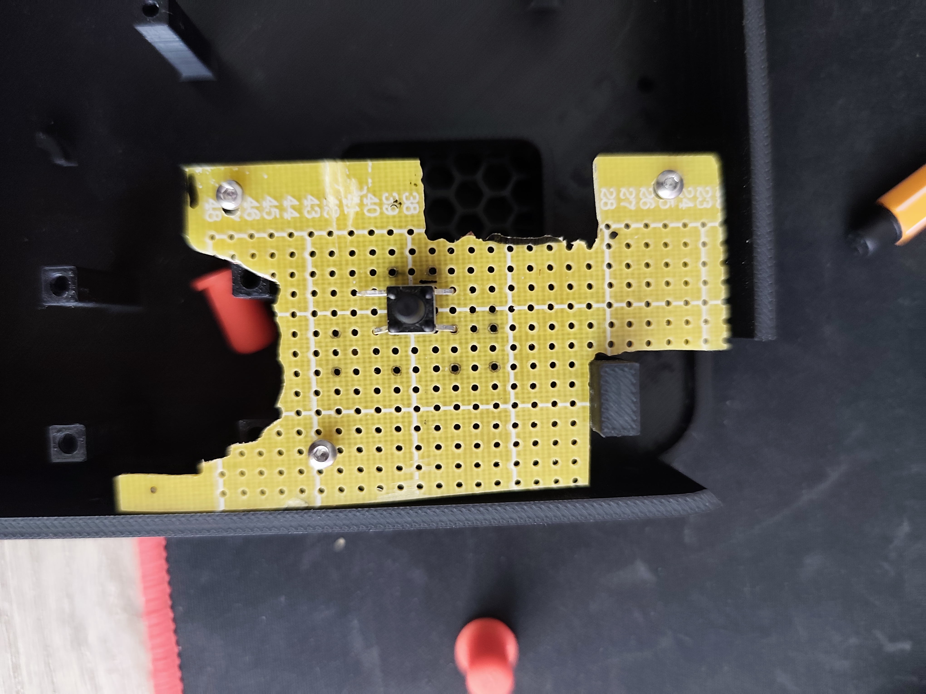
Media/photos/IMG_20260314_141306.jpg
