Klesp0/Bigtendo-Handheld-SBC/Media/photos/IMG_20260314_142848.jpg

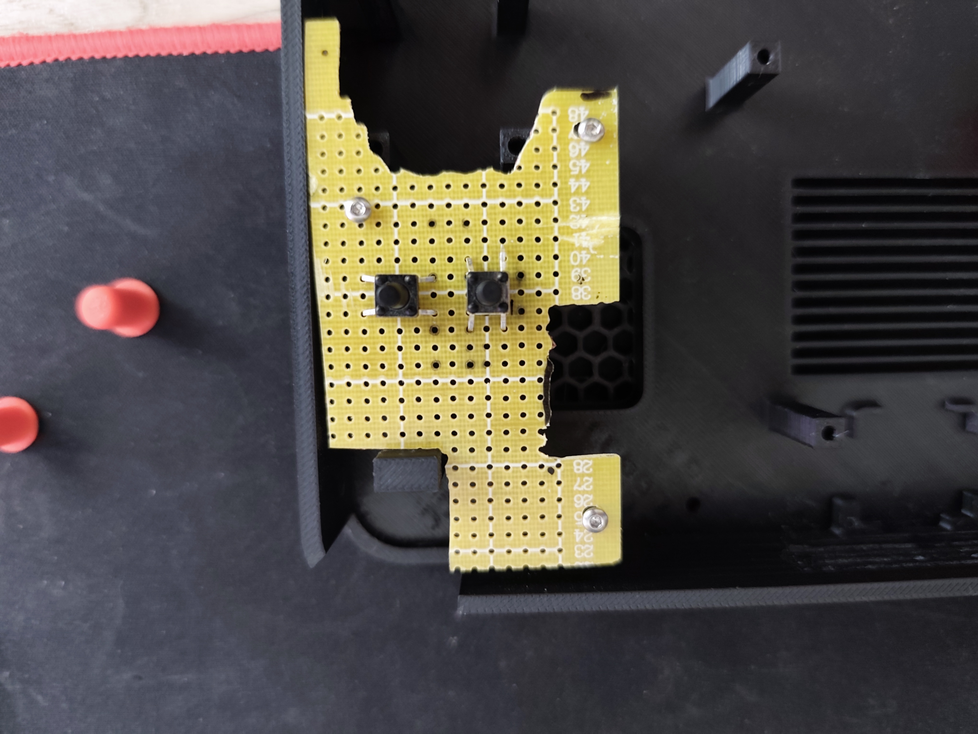
Media/photos/IMG_20260314_142848.jpg
