Klesp0/Bigtendo-Handheld-SBC/Media/photos/IMG_20260316_152539.jpg

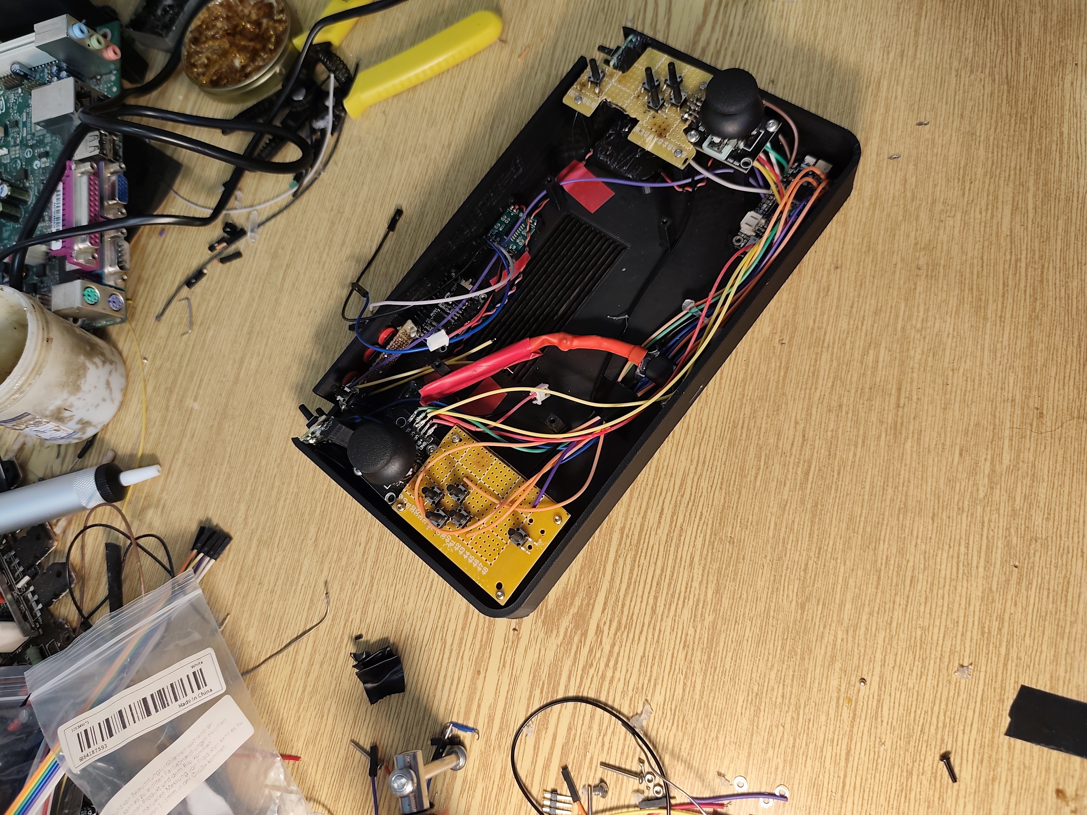
Media/photos/IMG_20260316_152539.jpg
