Klesp0/Bigtendo-Handheld-SBC/Media/photos/IMG_20260316_152543.jpg

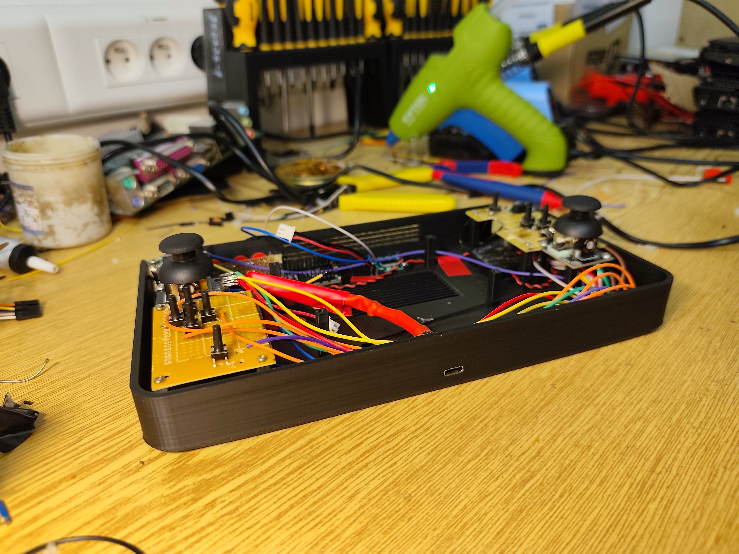
Media/photos/IMG_20260316_152543.jpg
