Klesp0/Bigtendo-Handheld-SBC/Media/photos/IMG_20260323_180728.jpg

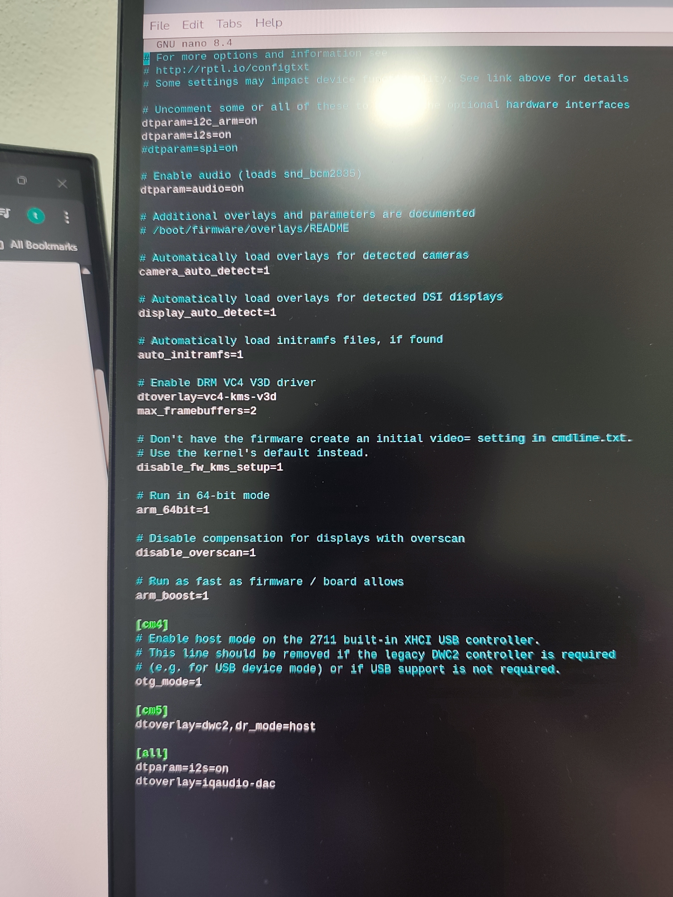
Media/photos/IMG_20260323_180728.jpg
