Klesp0/Bigtendo-Handheld-SBC/Media/photos/rn_image_picker_lib_temp_0d362930-16ea-474a-9831-ca31197bad1f(1).jpg

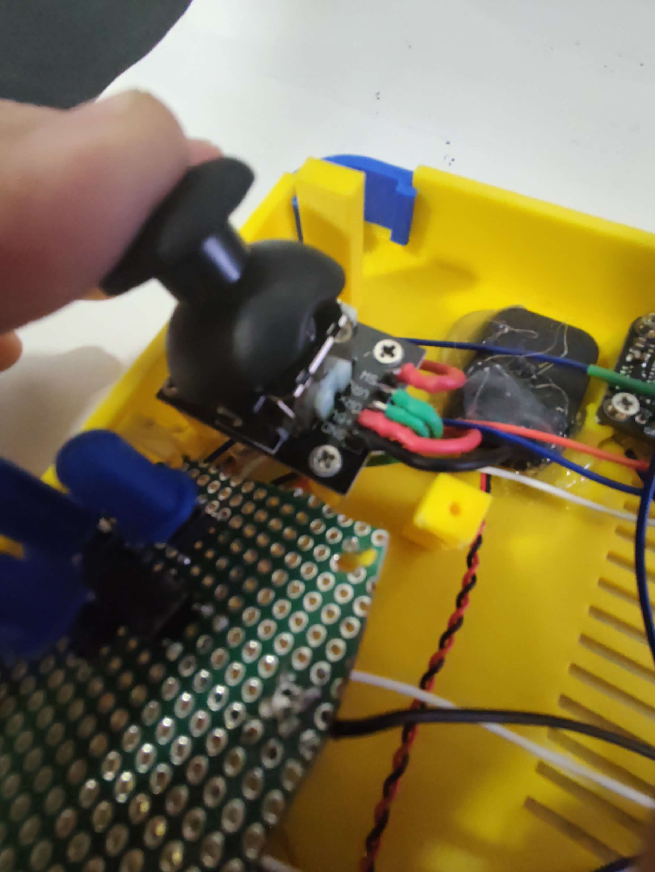
Media/photos/rn_image_picker_lib_temp_0d362930-16ea-474a-9831-ca31197bad1f(1).jpg
