Klesp0/Bigtendo-Handheld-SBC/Media/photos/schéma_kontroléra1.png

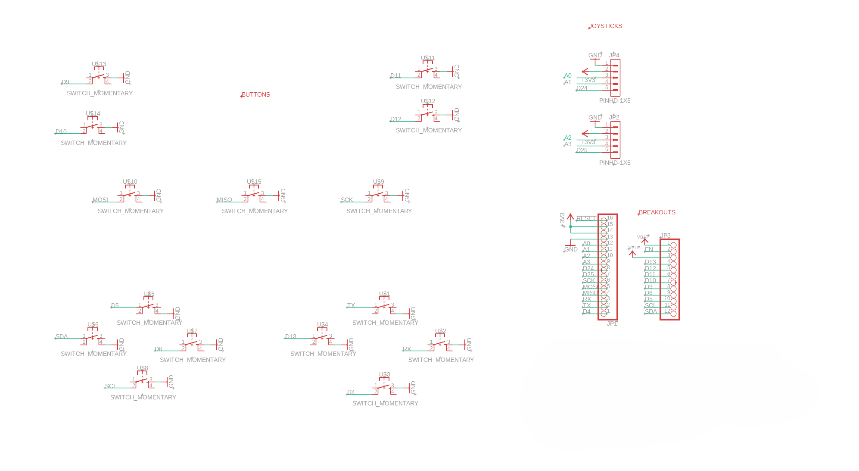
Media/photos/schéma_kontroléra1.png
