Klesp0/Bigtendo-Handheld-SBC/Media/photos/Screenshot 2026-03-13 201316.png

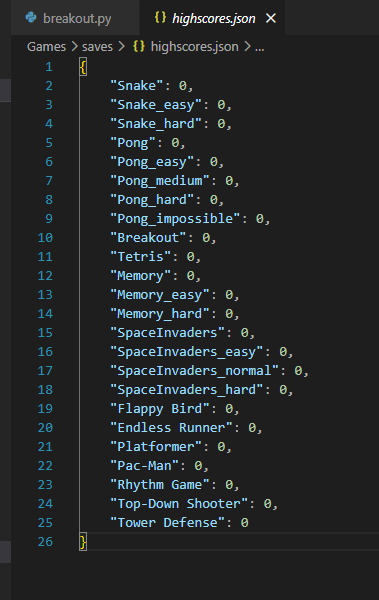
Media/photos/Screenshot 2026-03-13 201316.png
