Klesp0/Bigtendo-Handheld-SBC/Design/3D_Models/component_models/amplfier PAM8403 3W.step

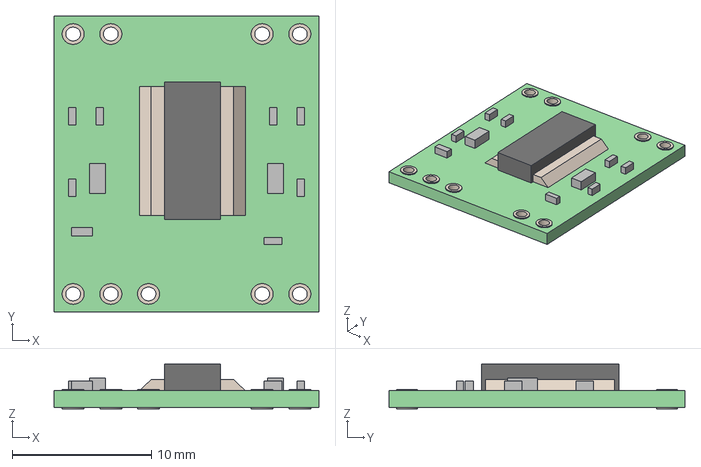
[picture p83: CAD file, 2026-05-09]
Design/3D_Models/component_models/amplfier PAM8403 3W.step
19.0 x 21.2 x 3.20 mm
