Klesp0/Bigtendo-Handheld-SBC/Design/3D_Models/component_models/USB Connector Type C female.STEP

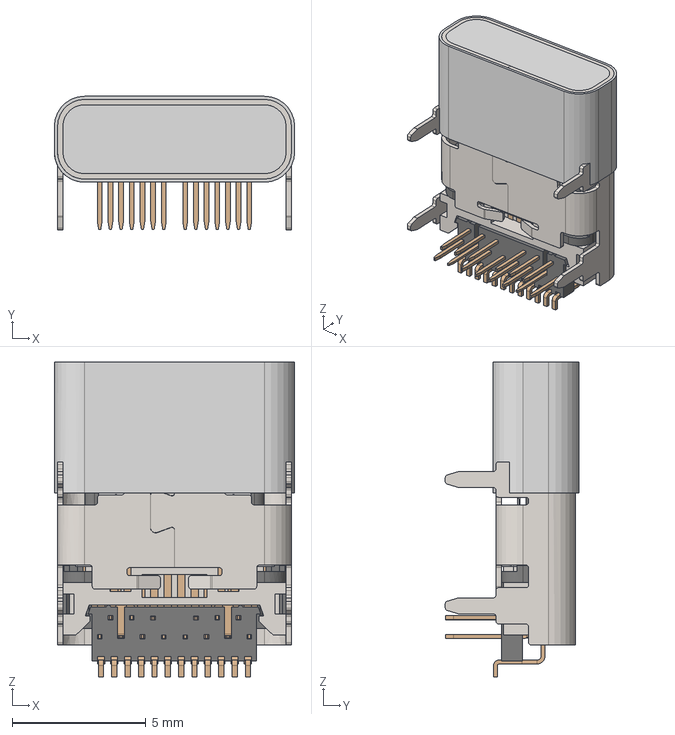
[picture p84: CAD file, 2026-05-09]
Design/3D_Models/component_models/USB Connector Type C female.STEP
9.00 x 5.00 x 11.8 mm
