Klesp0/Bigtendo-Handheld-SBC/Design/3D_Models/component_models/joystick.step

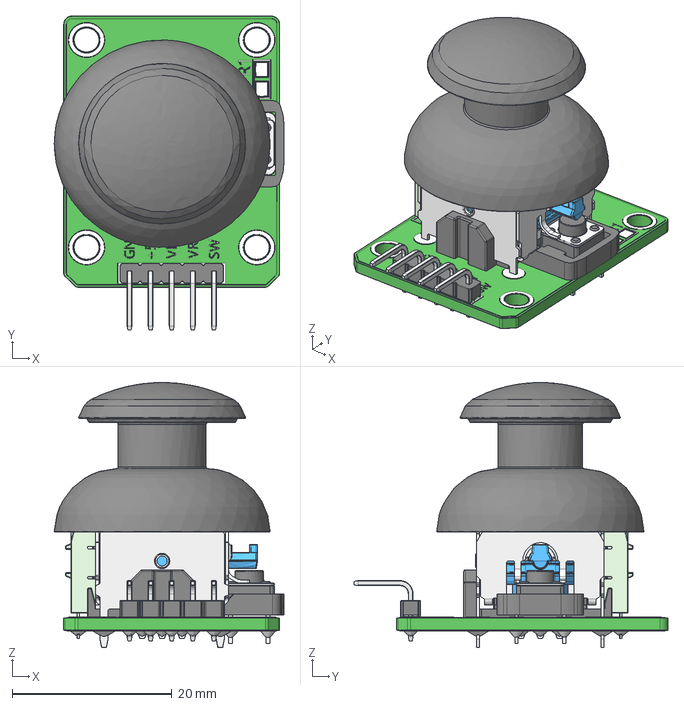
[picture p85: CAD file, 2026-05-09]
Design/3D_Models/component_models/joystick.step
28.8 x 39.4 x 33.2 mm
