Klesp0/Bigtendo-Handheld-SBC/Media/photos/wiring/breakout.png

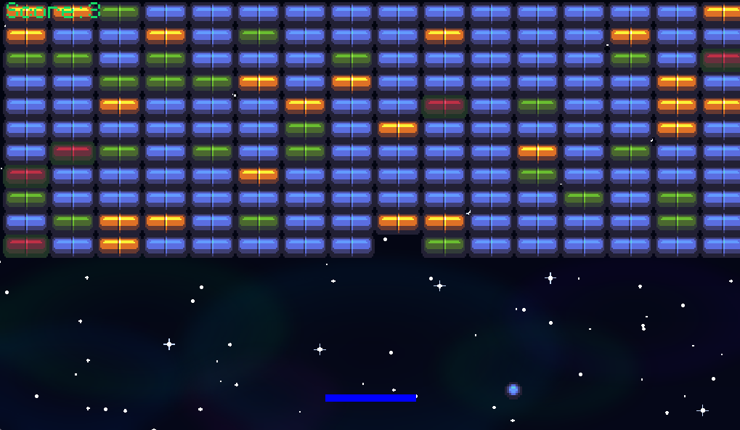
Media/photos/wiring/breakout.png
