Klesp0/Bigtendo-Handheld-SBC/Media/photos/wiring/cool.jpg

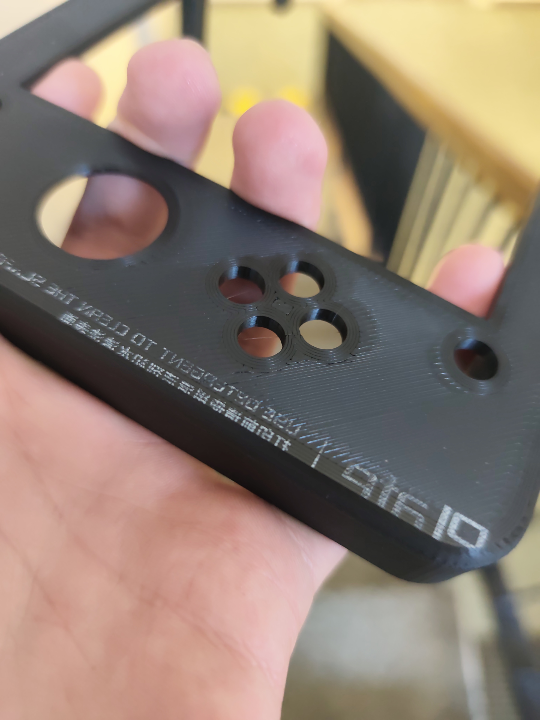
Media/photos/wiring/cool.jpg
