Klesp0/Bigtendo-Handheld-SBC/Media/photos/wiring/mega3.jpg

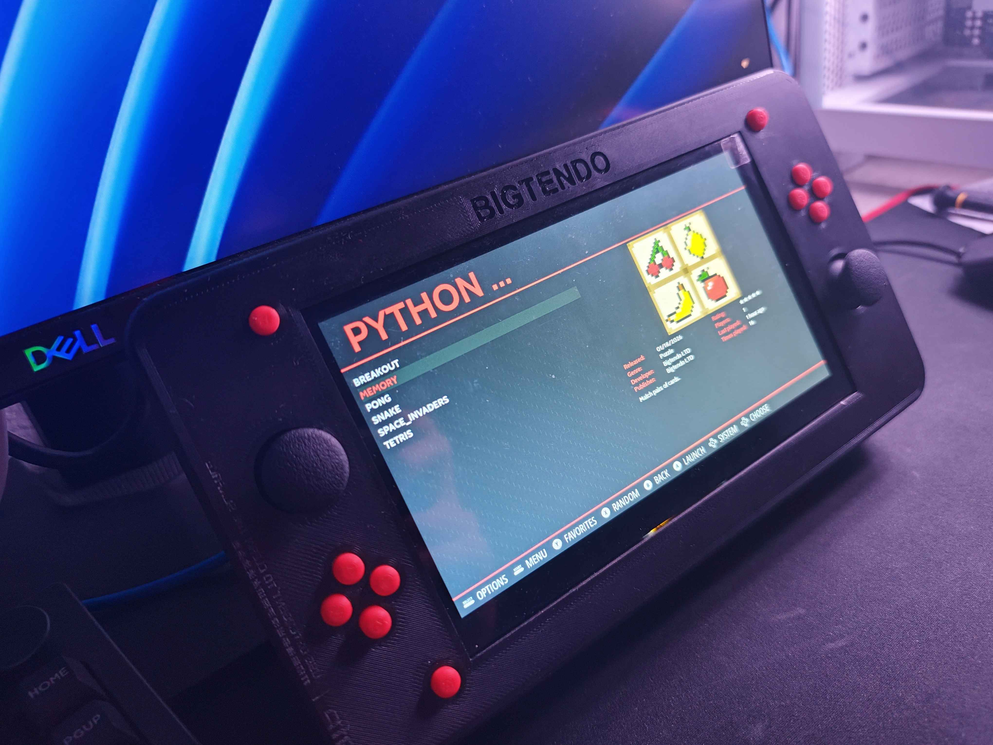
Media/photos/wiring/mega3.jpg
