Klesp0/Bigtendo-Handheld-SBC/Media/photos/wiring/random.jpg

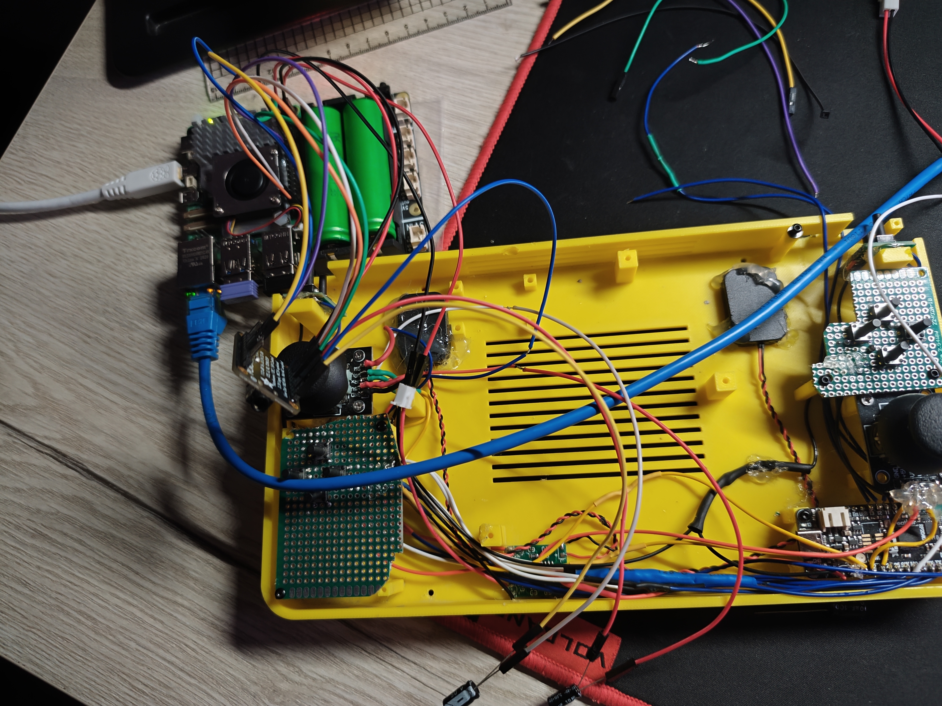
Media/photos/wiring/random.jpg
