Klesp0/Bigtendo-Handheld-SBC/Media/photos/wiring/rpi_ups.jpg

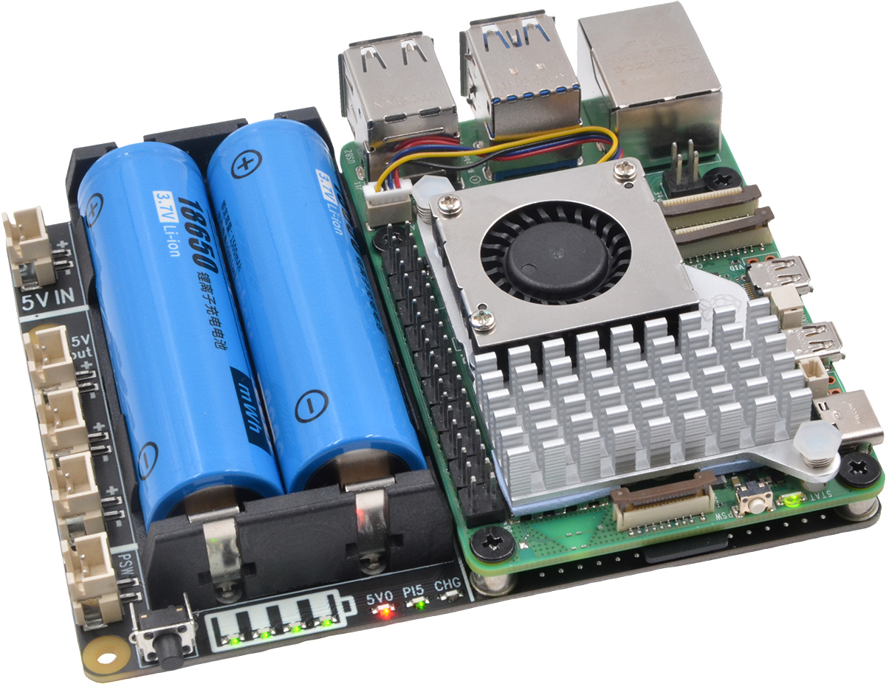
Media/photos/wiring/rpi_ups.jpg
