Klesp0/Bigtendo-Handheld-SBC/Media/photos/wiring/urcite.jpg

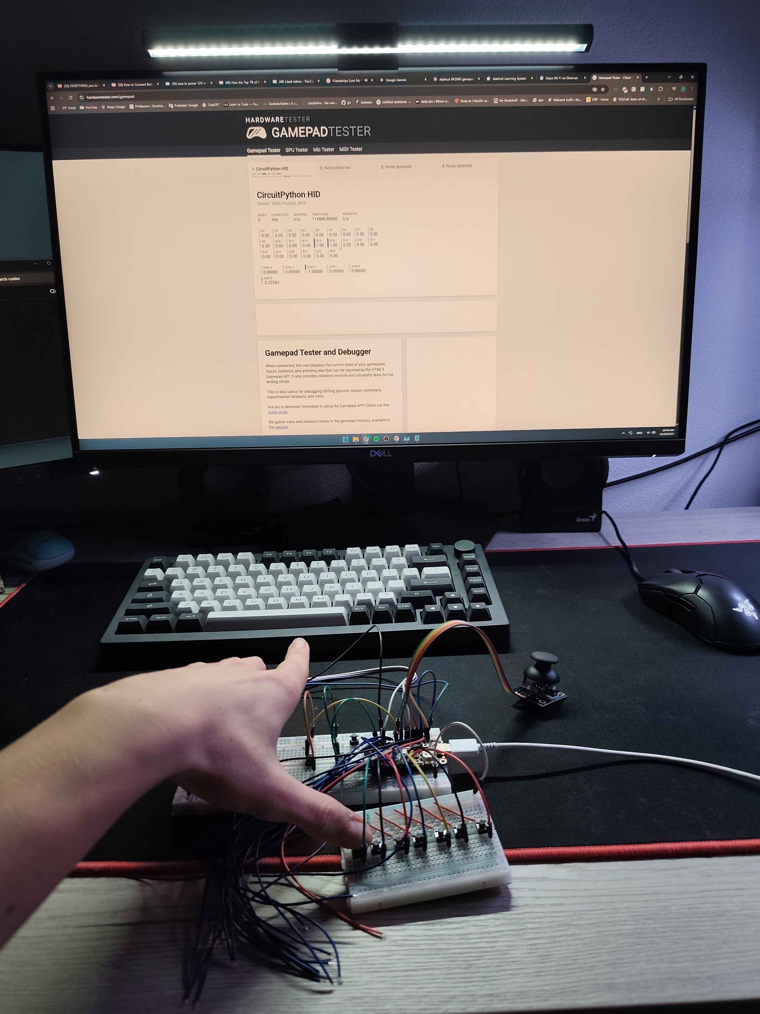
Media/photos/wiring/urcite.jpg
