Klesp0/Bigtendo-Handheld-SBC/Media/photos/wiring/test.jpg

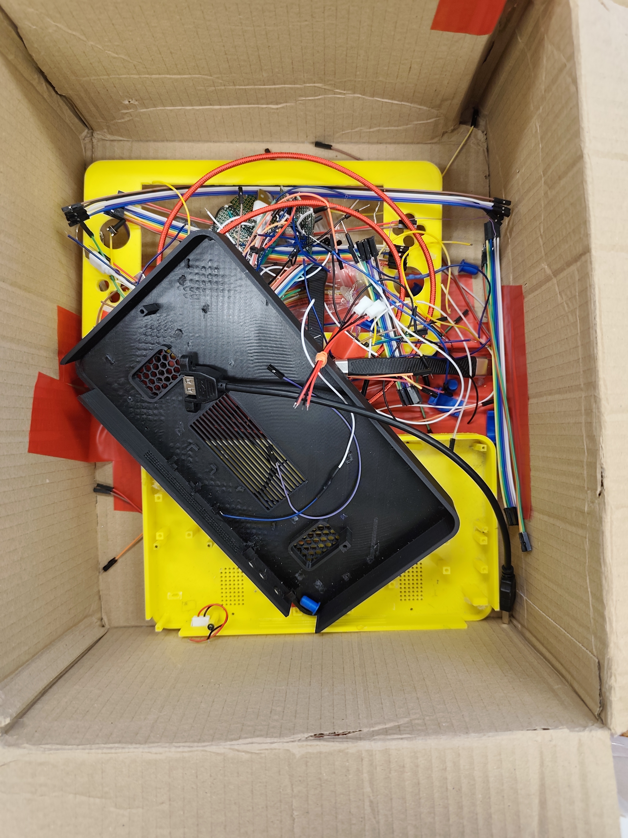
Media/photos/wiring/test.jpg
